HaroldMurcia/AgroSenseV1.0/Diseño/Capturas Corriente/GAS0001.BMP

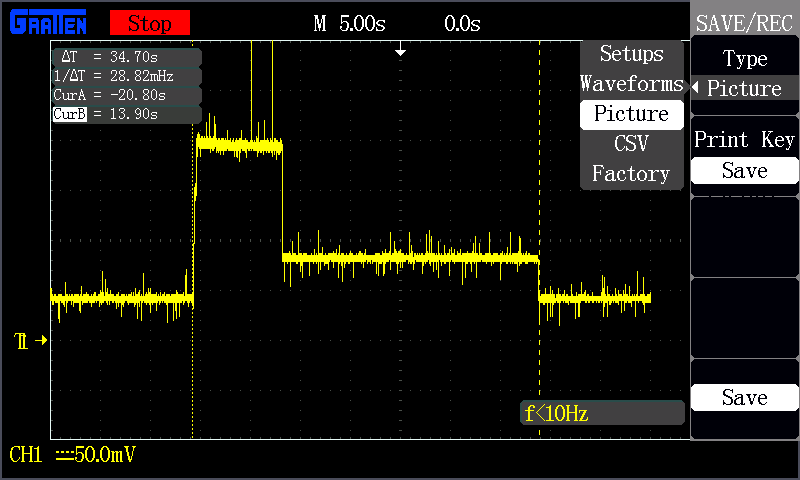
Diseño/Capturas Corriente/GAS0001.BMP
