HaroldMurcia/AgroSenseV1.0/Media/1537698291_831325_1537698456_noticia_normal.jpg

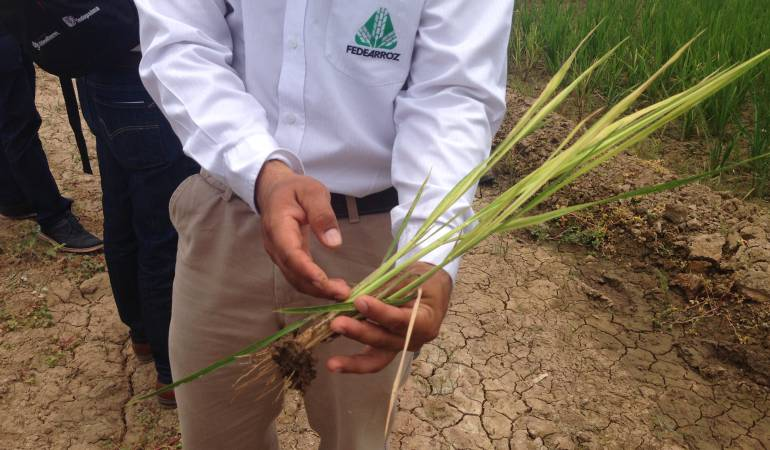
Media/1537698291_831325_1537698456_noticia_normal.jpg
