HaroldMurcia/AgroSenseV1.0/Media/1537698291_831325_1537700034_sumario_normal.jpg

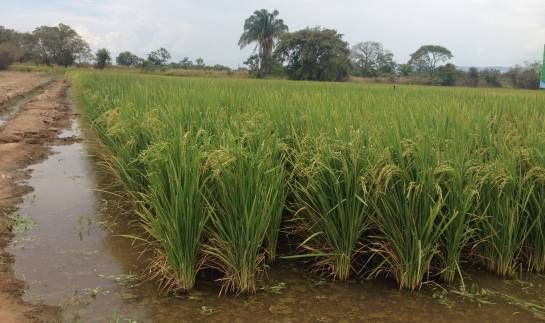
Media/1537698291_831325_1537700034_sumario_normal.jpg
