HaroldMurcia/AgroSenseV1.0/Media/AgroS.004.jpg

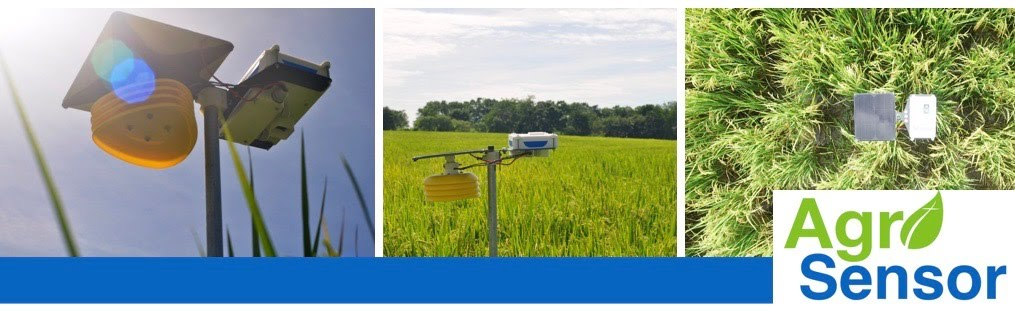
Media/AgroS.004.jpg
