HaroldMurcia/AgroSenseV1.0/Media/Agrosensor2.jpg

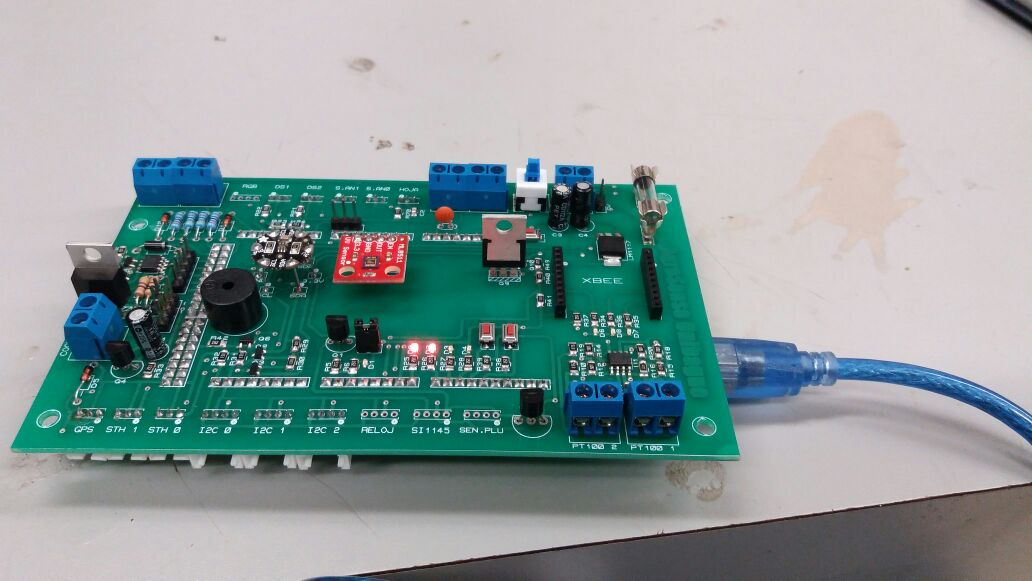
Media/Agrosensor2.jpg
