HaroldMurcia/AgroSenseV1.0/Media/Agrosensor Collector.PNG

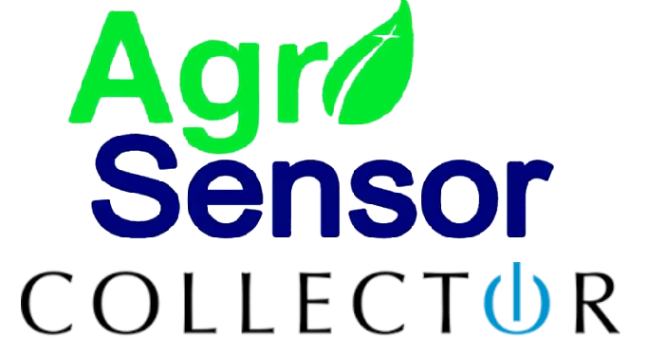
Media/Agrosensor Collector.PNG
