HaroldMurcia/AgroSenseV1.0/Media/Agrosensor.jpg

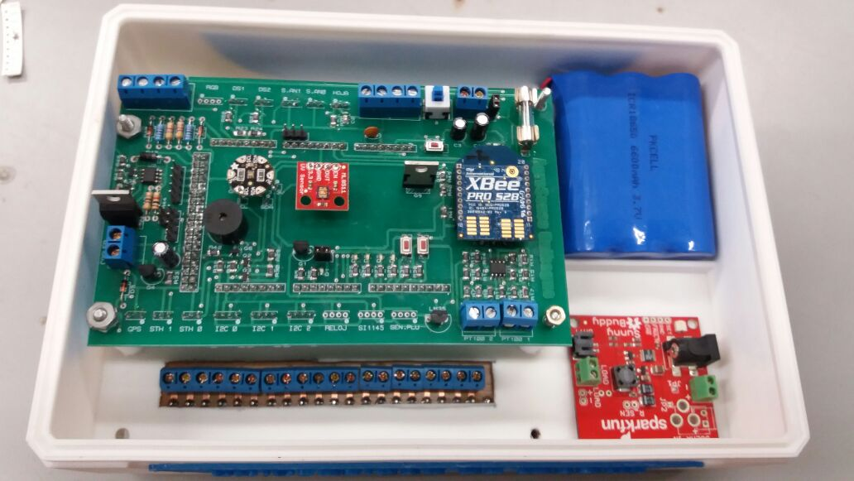
Media/Agrosensor.jpg
