HaroldMurcia/AgroSenseV1.0/Media/Configuracion XBee/Firmware Colector.jpg

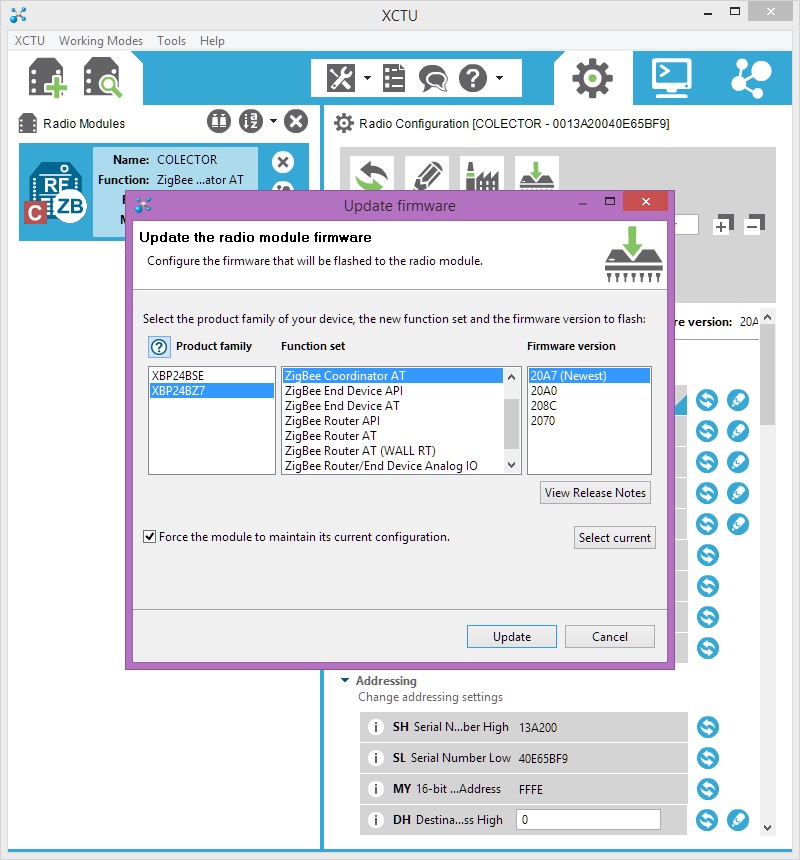
Media/Configuracion XBee/Firmware Colector.jpg
