HaroldMurcia/AgroSenseV1.0/Media/Configuracion XBee/Firmware Nodo.jpg

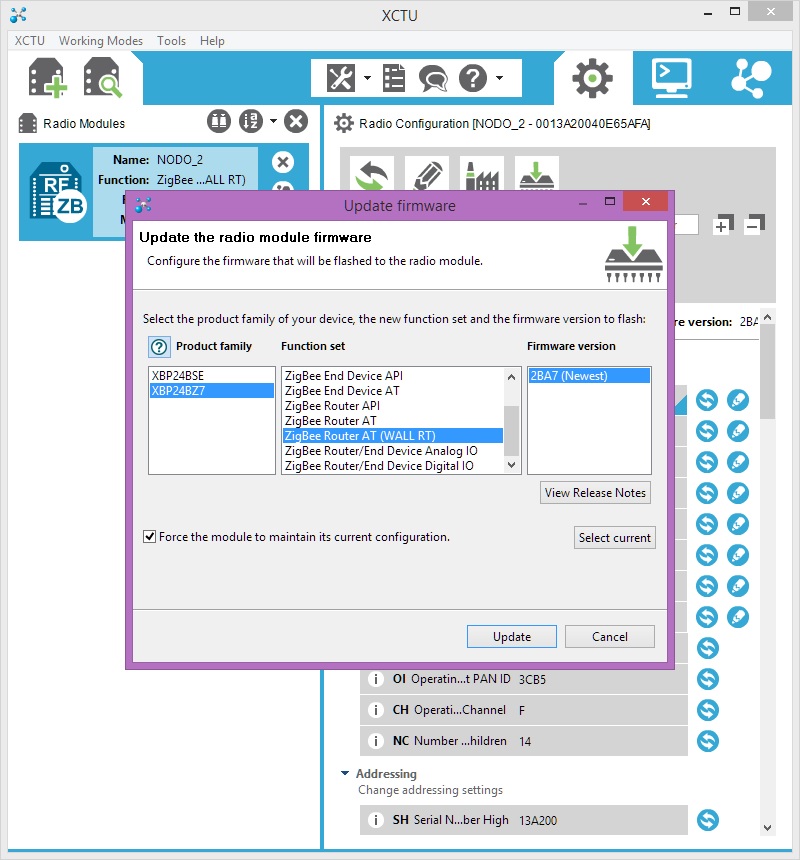
Media/Configuracion XBee/Firmware Nodo.jpg
