HaroldMurcia/AgroSenseV1.0/Media/DS18B20 grafica.jpg

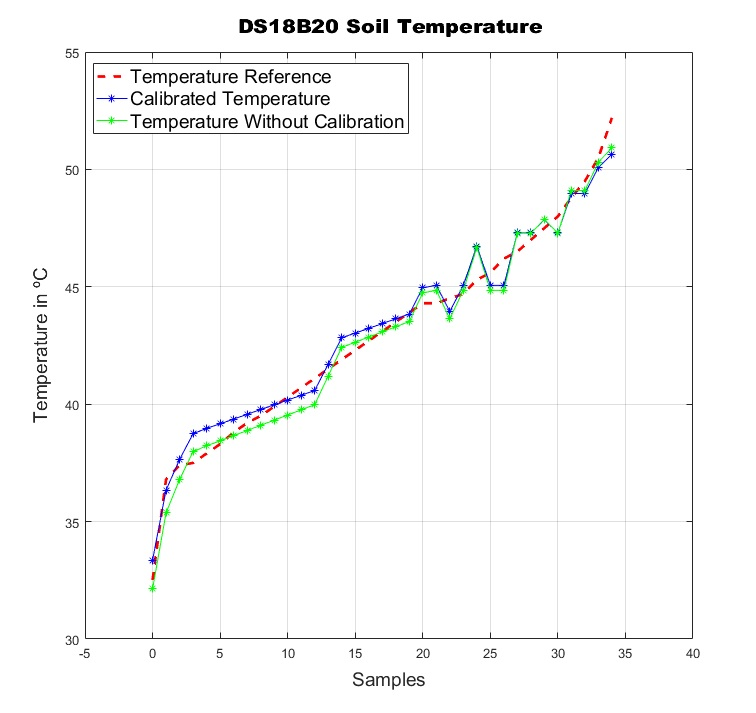
Media/DS18B20 grafica.jpg
