HaroldMurcia/AgroSenseV1.0/Media/DSC_0012.JPG

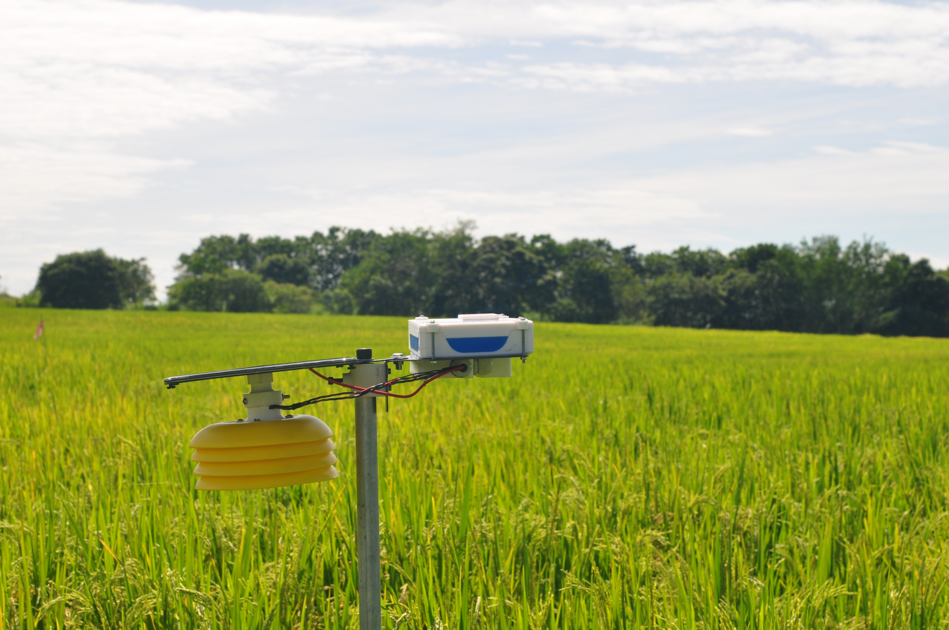
Media/DSC_0012.JPG
