HaroldMurcia/AgroSenseV1.0/Media/DSC_0013.JPG

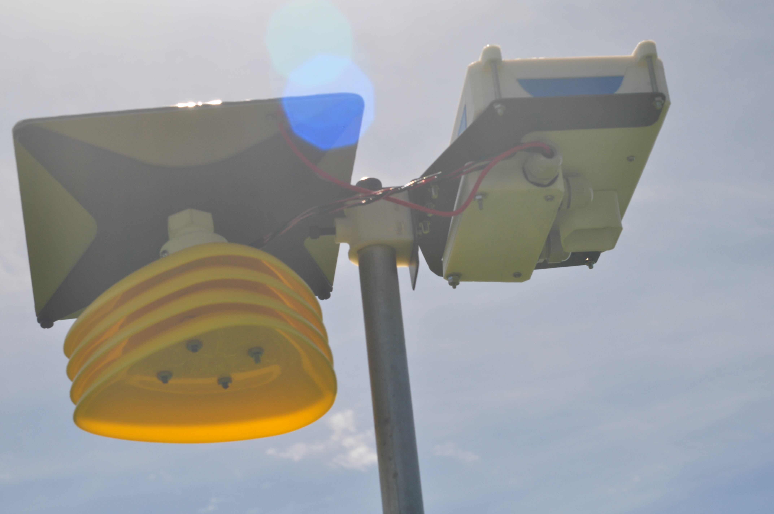
Media/DSC_0013.JPG
