HaroldMurcia/AgroSenseV1.0/Media/DSC_0014.JPG

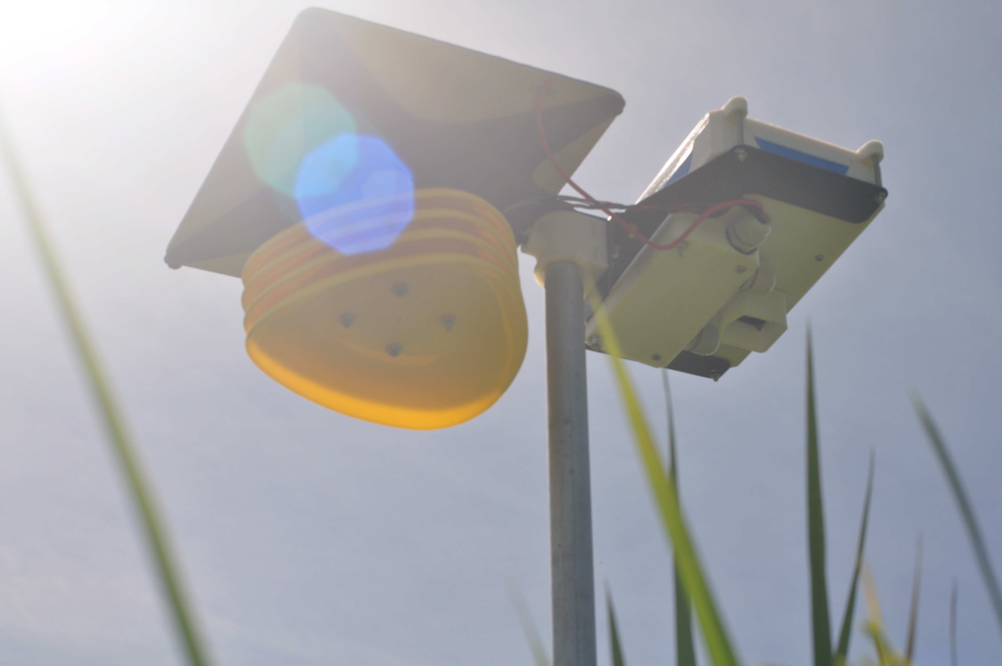
Media/DSC_0014.JPG
