HaroldMurcia/AgroSenseV1.0/Media/DSC_0015.JPG

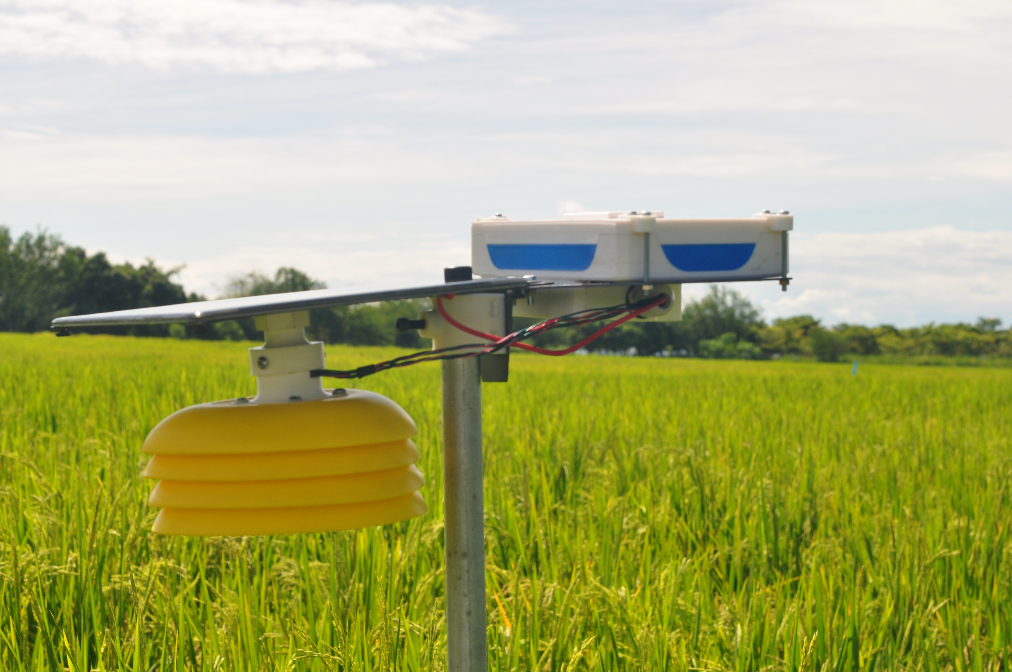
Media/DSC_0015.JPG
