HaroldMurcia/AgroSenseV1.0/Media/Fotos.jpg

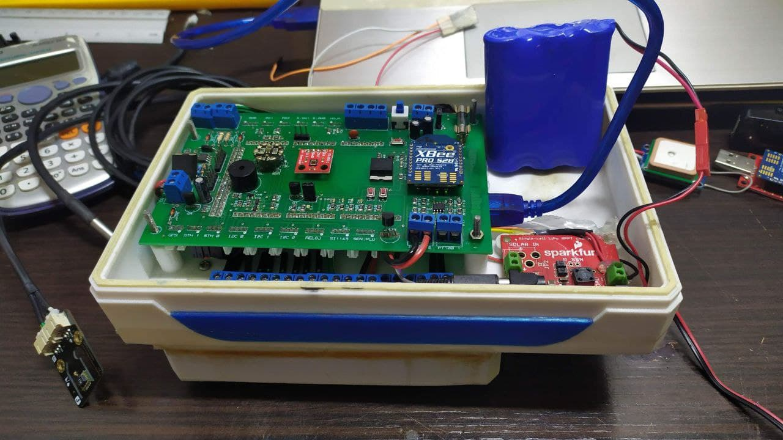
Media/Fotos.jpg
