HaroldMurcia/AgroSenseV1.0/Media/Grafica1.jpg

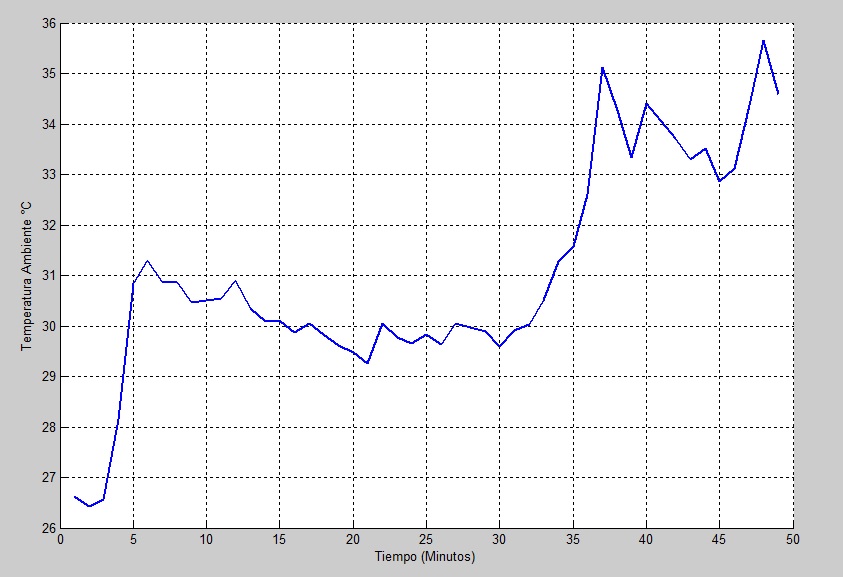
Media/Grafica1.jpg
