HaroldMurcia/AgroSenseV1.0/Media/Grafica2.jpg

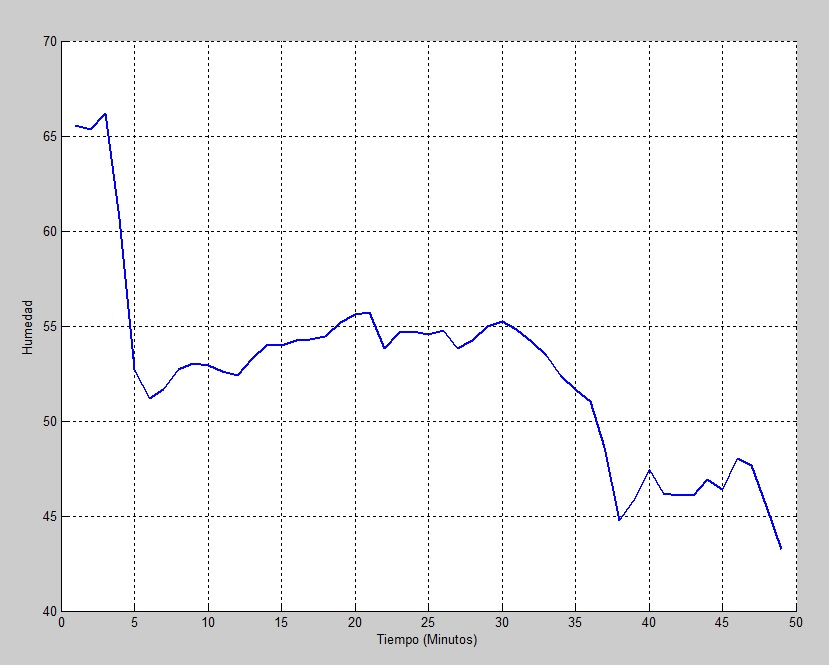
Media/Grafica2.jpg
