HaroldMurcia/AgroSenseV1.0/Media/Grafica3.jpg

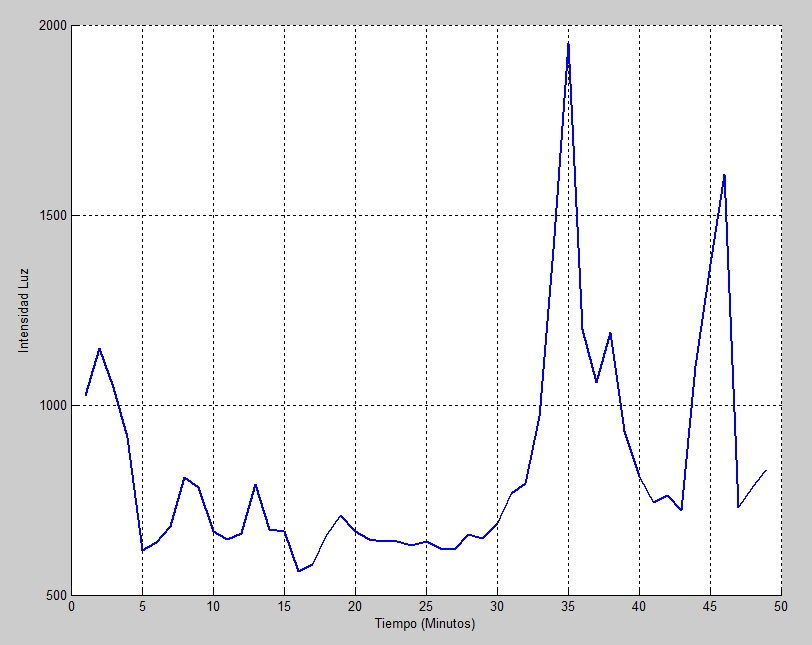
Media/Grafica3.jpg
