HaroldMurcia/AgroSenseV1.0/Media/Grafica4.jpg

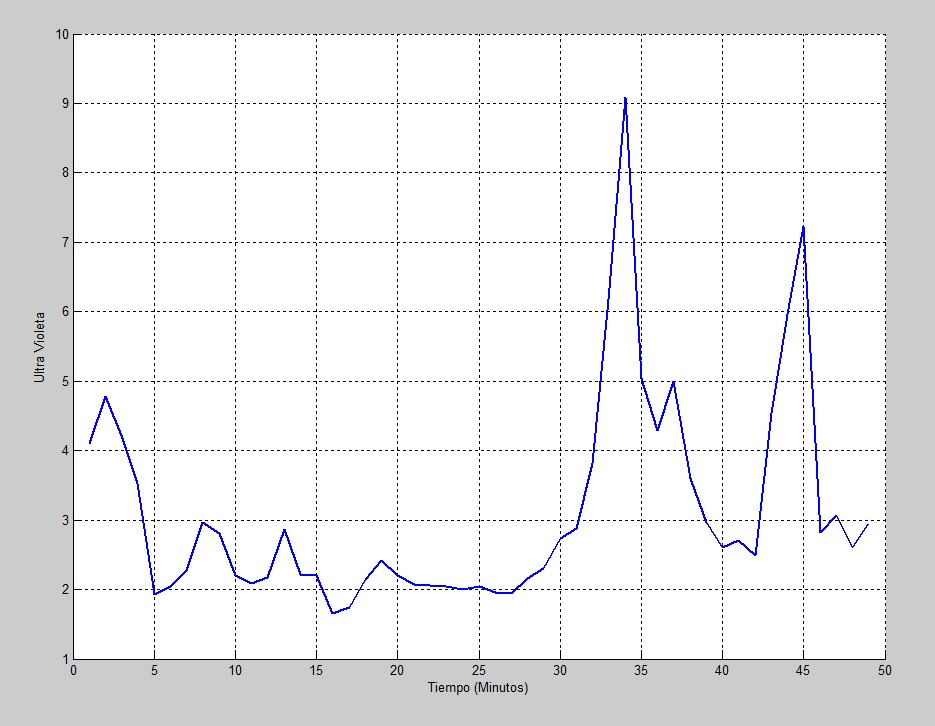
Media/Grafica4.jpg
