HaroldMurcia/AgroSenseV1.0/Media/Grafica IV Panel.bmp

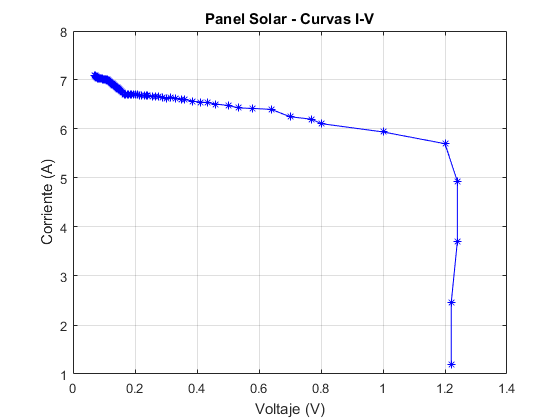
Media/Grafica IV Panel.bmp
