HaroldMurcia/AgroSenseV1.0/Media/image (1).png

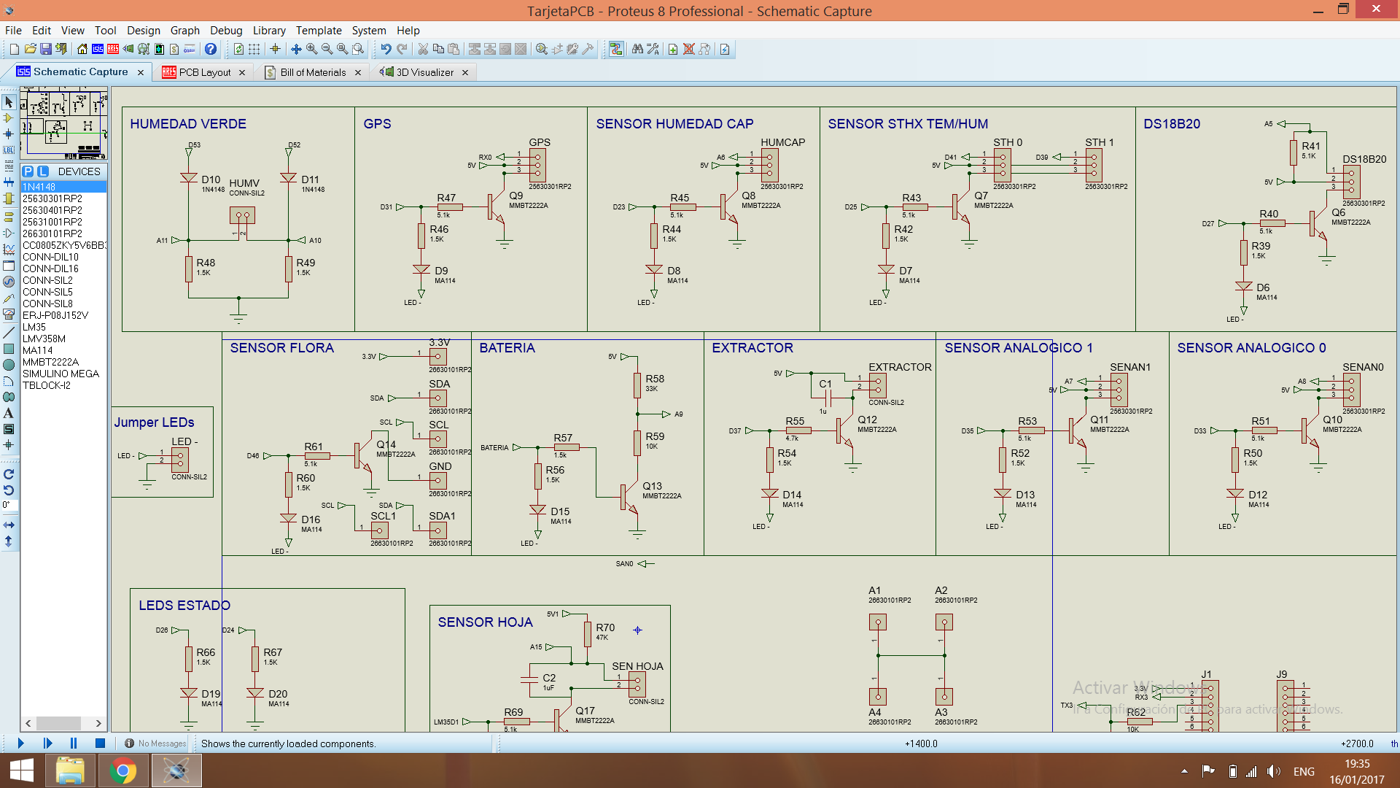
Media/image (1).png
