HaroldMurcia/AgroSenseV1.0/Media/image (2).png

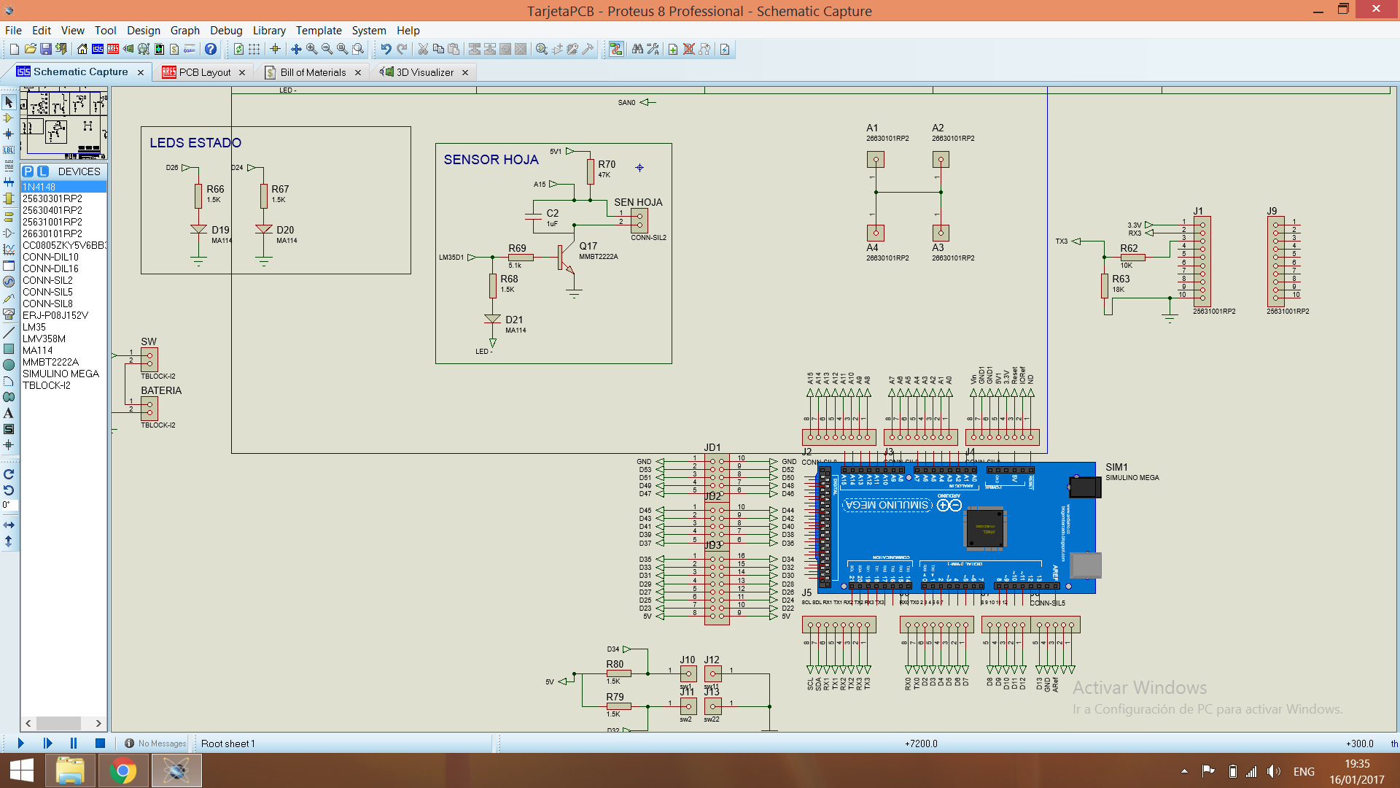
Media/image (2).png
