HaroldMurcia/AgroSenseV1.0/Media/image.png

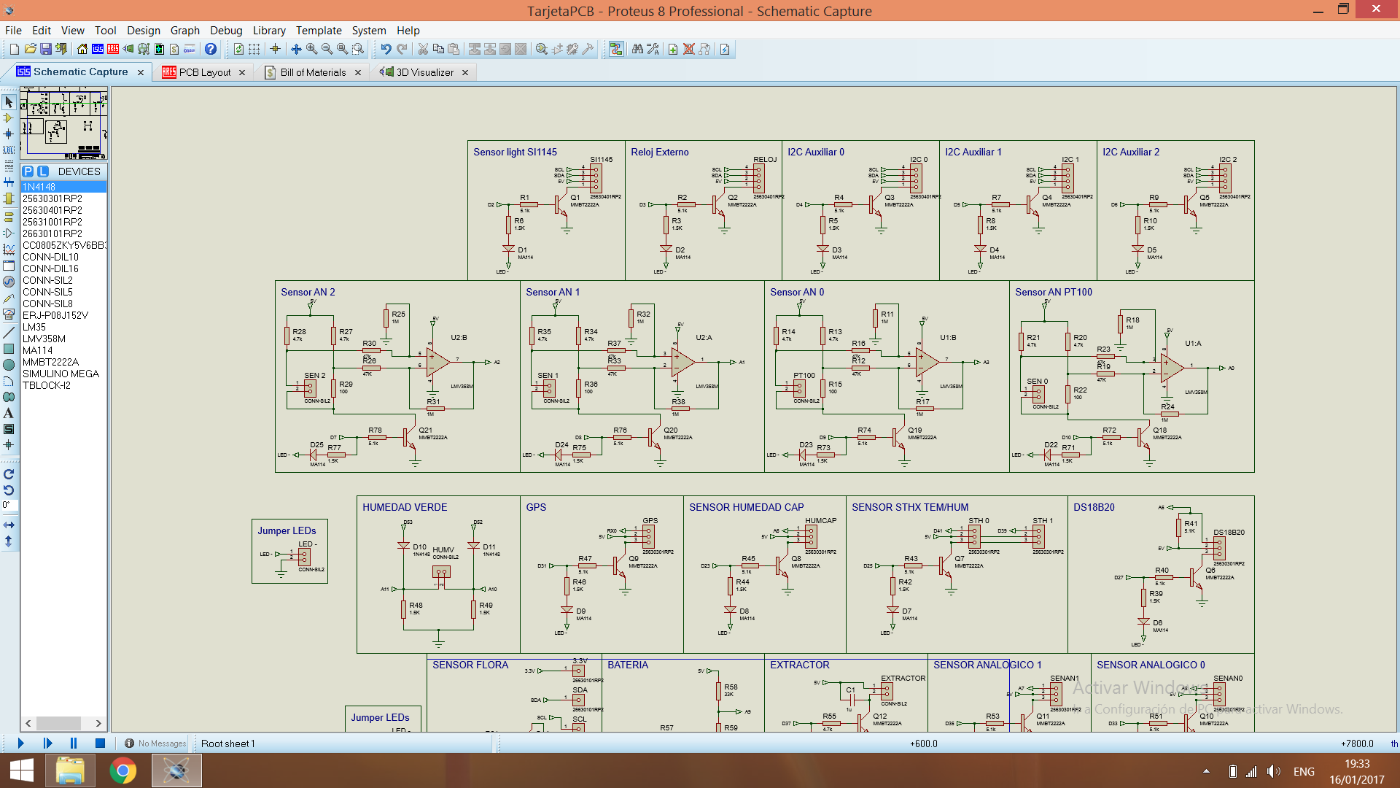
Media/image.png
