HaroldMurcia/AgroSenseV1.0/Media/IMG_3761.jpg

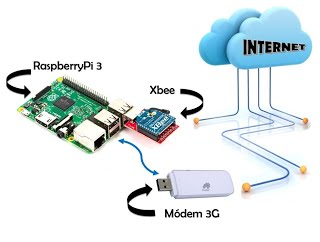
Media/IMG_3761.jpg
