HaroldMurcia/AgroSenseV1.0/Media/Mapa.png

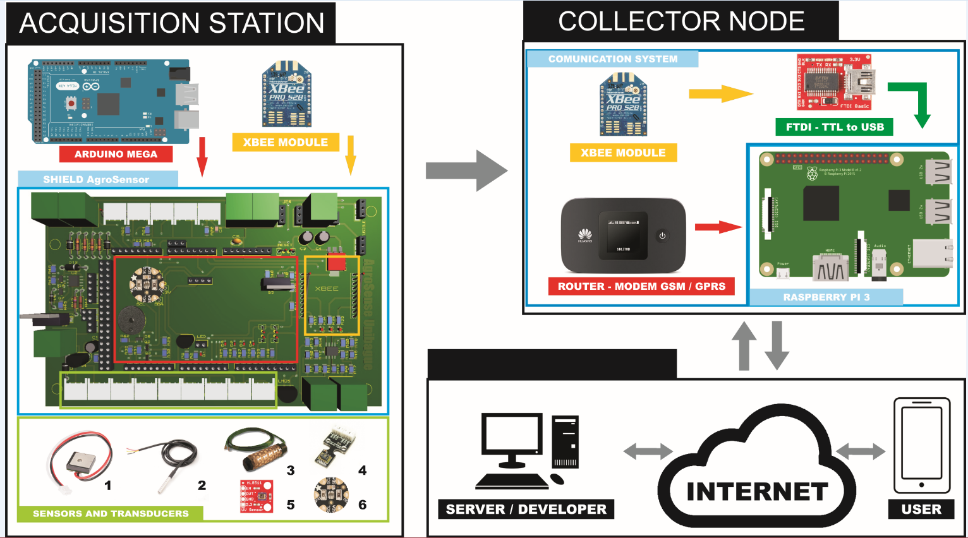
Media/Mapa.png
