HaroldMurcia/AgroSenseV1.0/Media/photo_2021-04-07_22-17-04.jpg

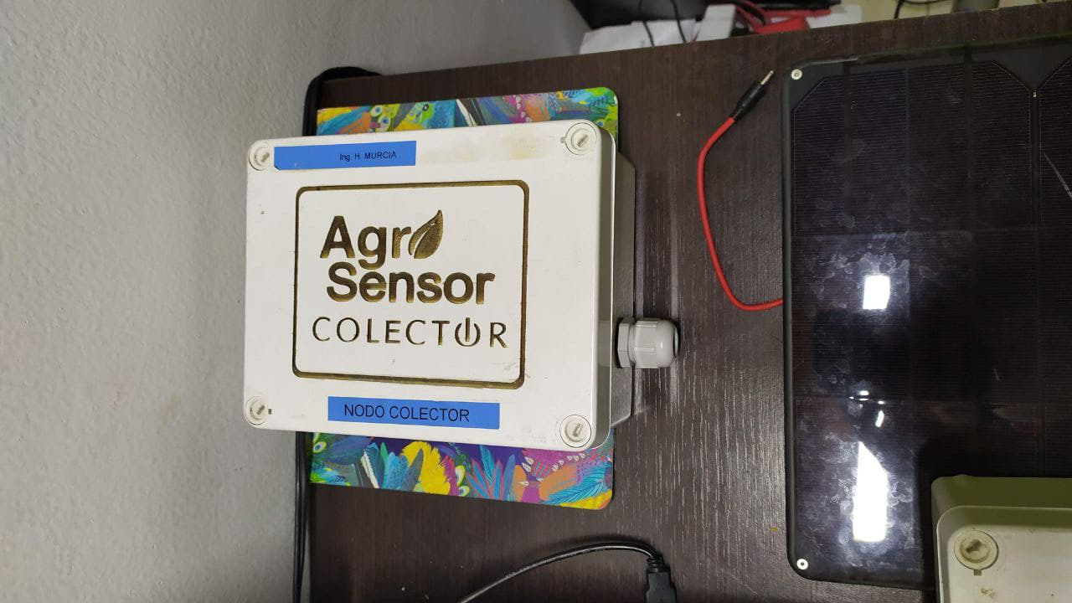
Media/photo_2021-04-07_22-17-04.jpg
