HaroldMurcia/AgroSenseV1.0/Media/Potencia.jpg

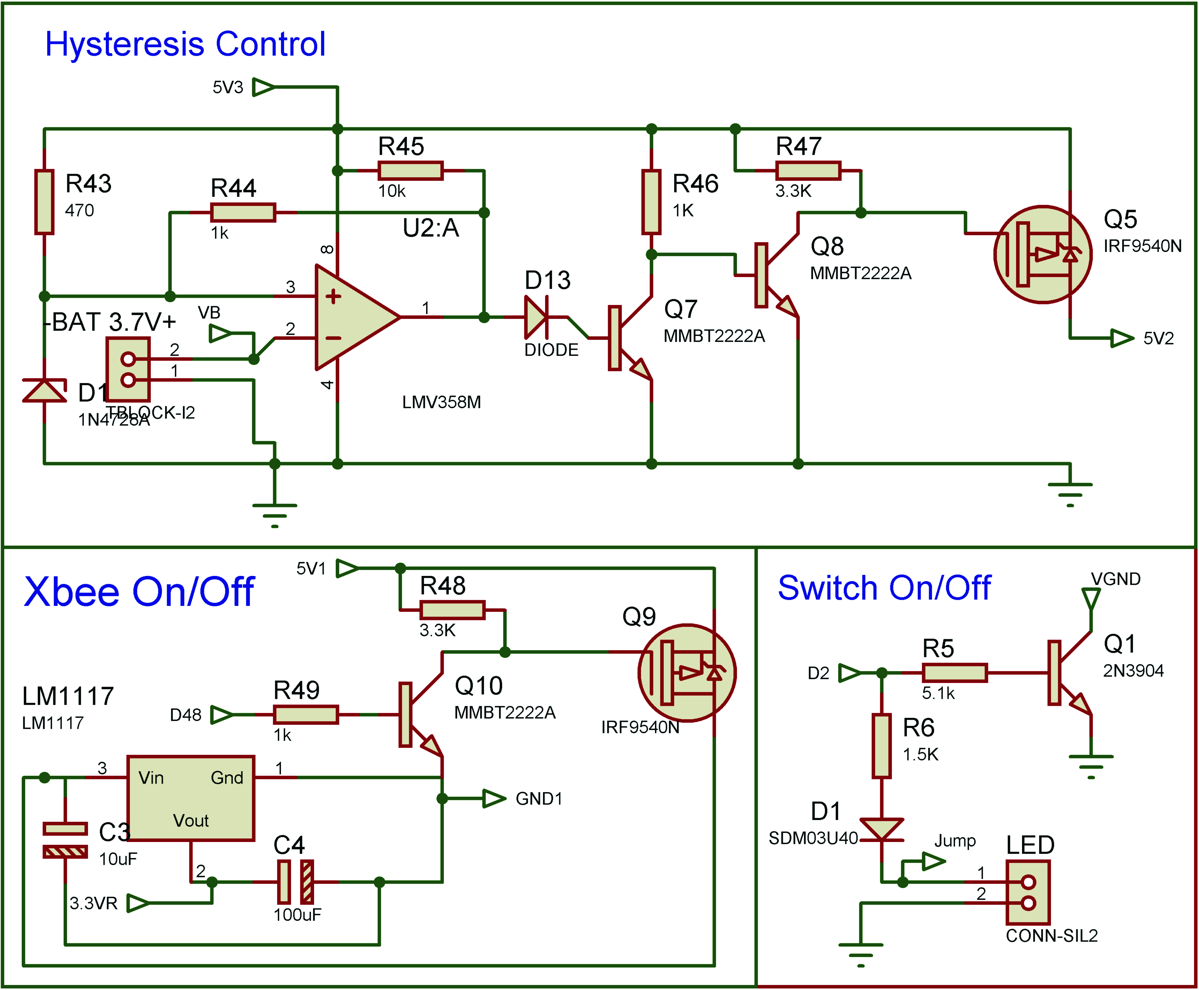
Media/Potencia.jpg
