HaroldMurcia/AgroSenseV1.0/Media/Prototipos/Codigo yowsup.png

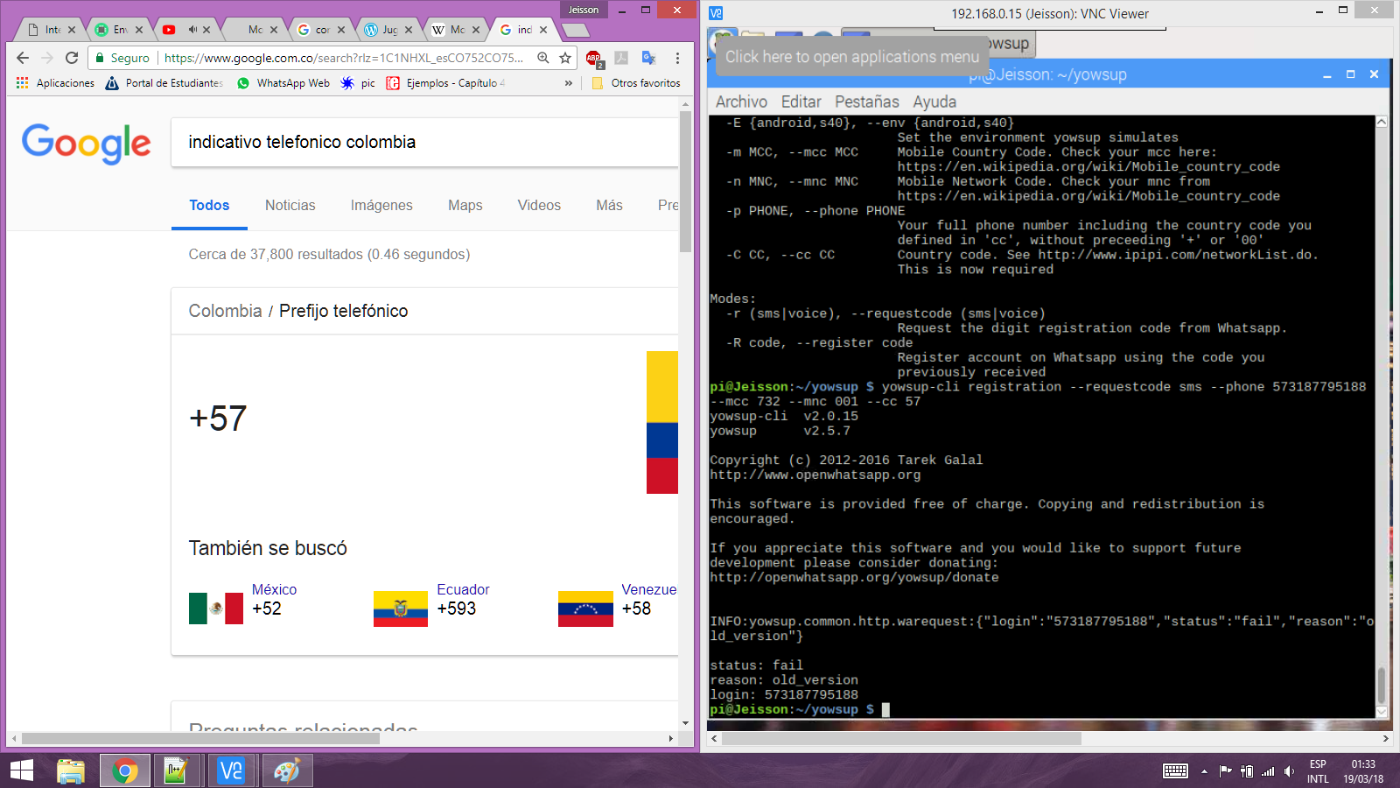
Media/Prototipos/Codigo yowsup.png
