HaroldMurcia/AgroSenseV1.0/Media/Prototipos/datod1.png

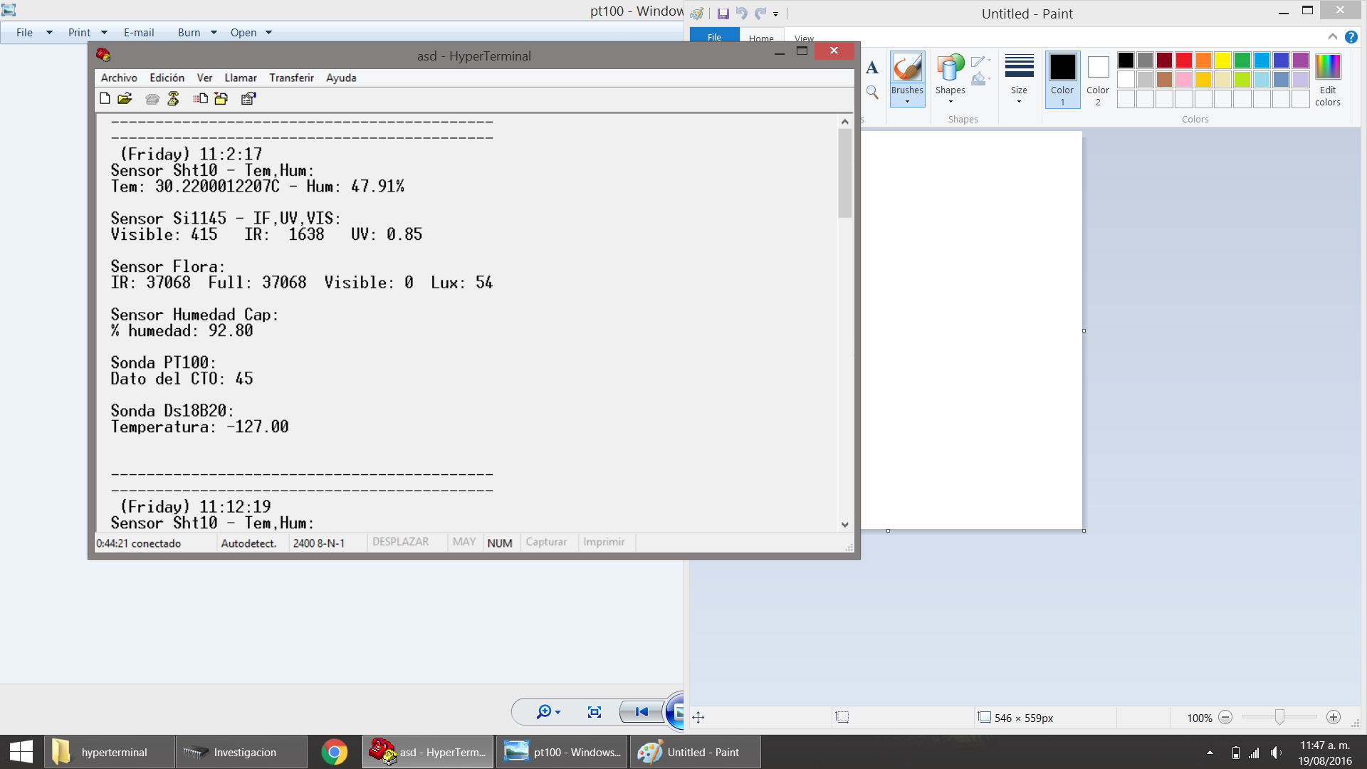
Media/Prototipos/datod1.png
