HaroldMurcia/AgroSenseV1.0/Media/Prototipos/datod2.png

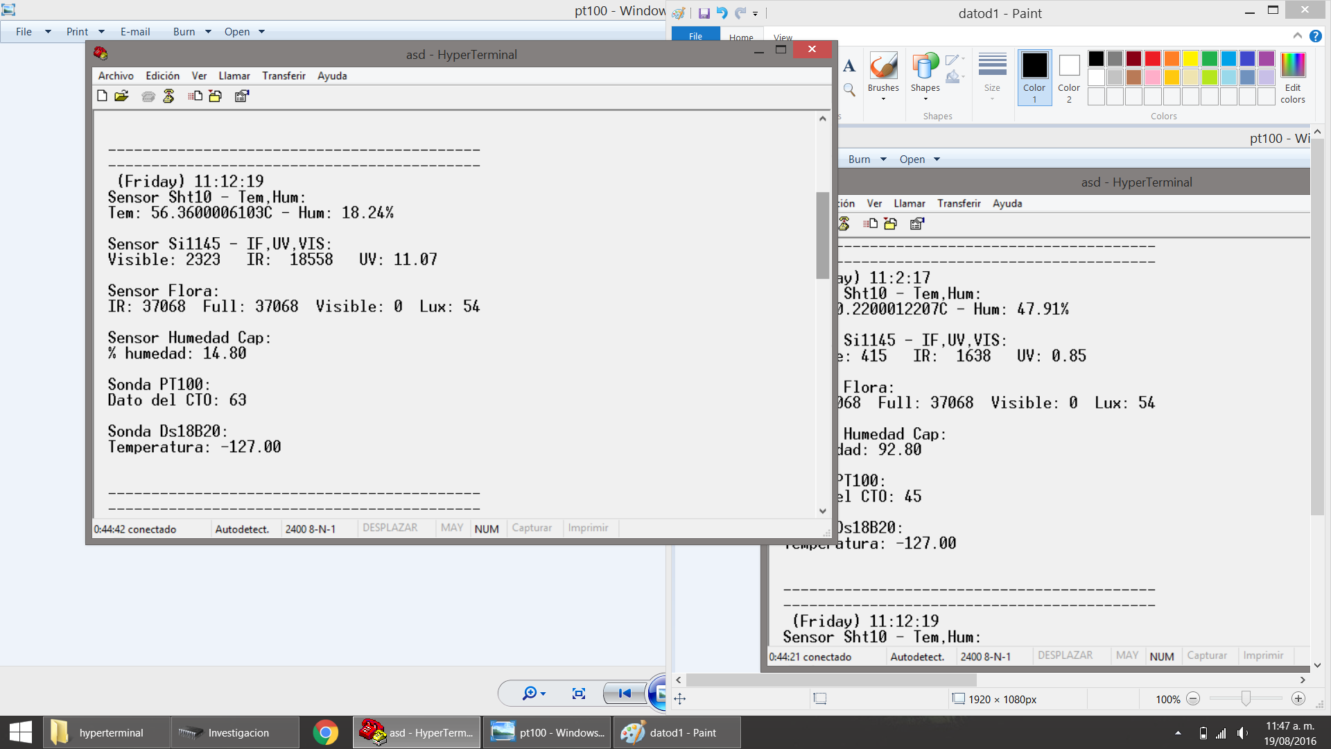
Media/Prototipos/datod2.png
