HaroldMurcia/AgroSenseV1.0/Media/Prototipos/datod3.png

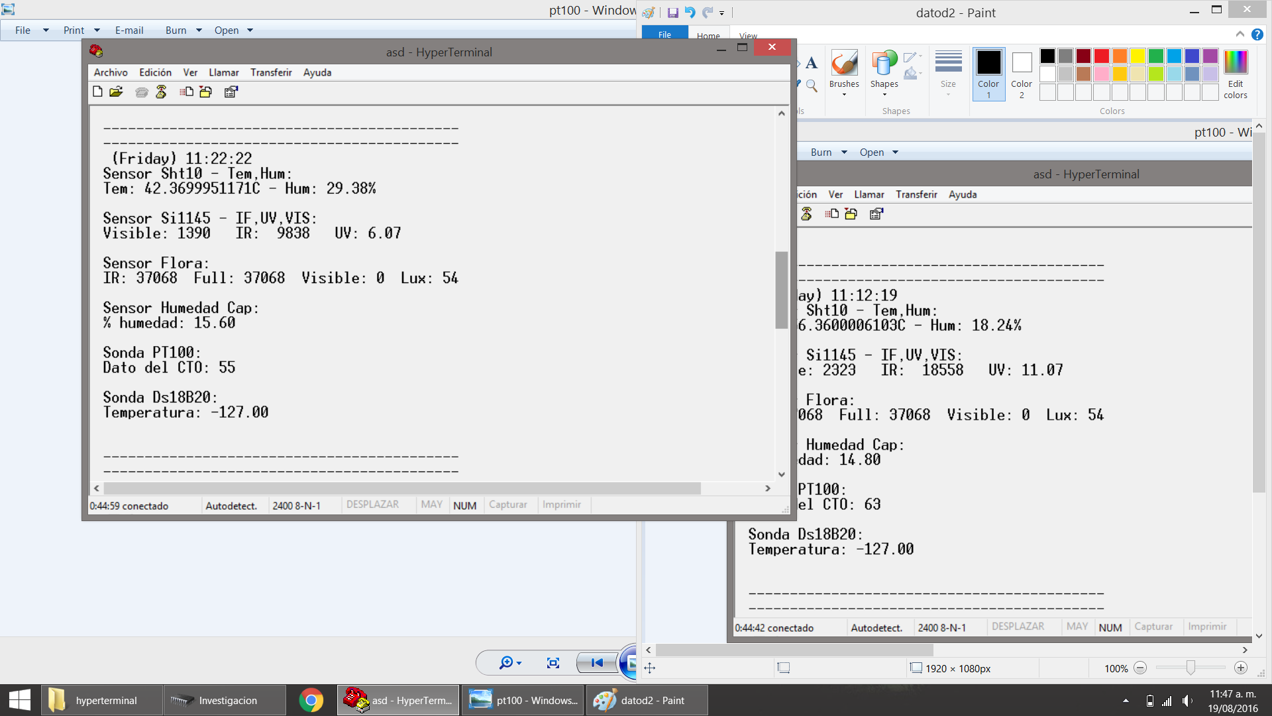
Media/Prototipos/datod3.png
