HaroldMurcia/AgroSenseV1.0/Media/Prototipos/datod5.png

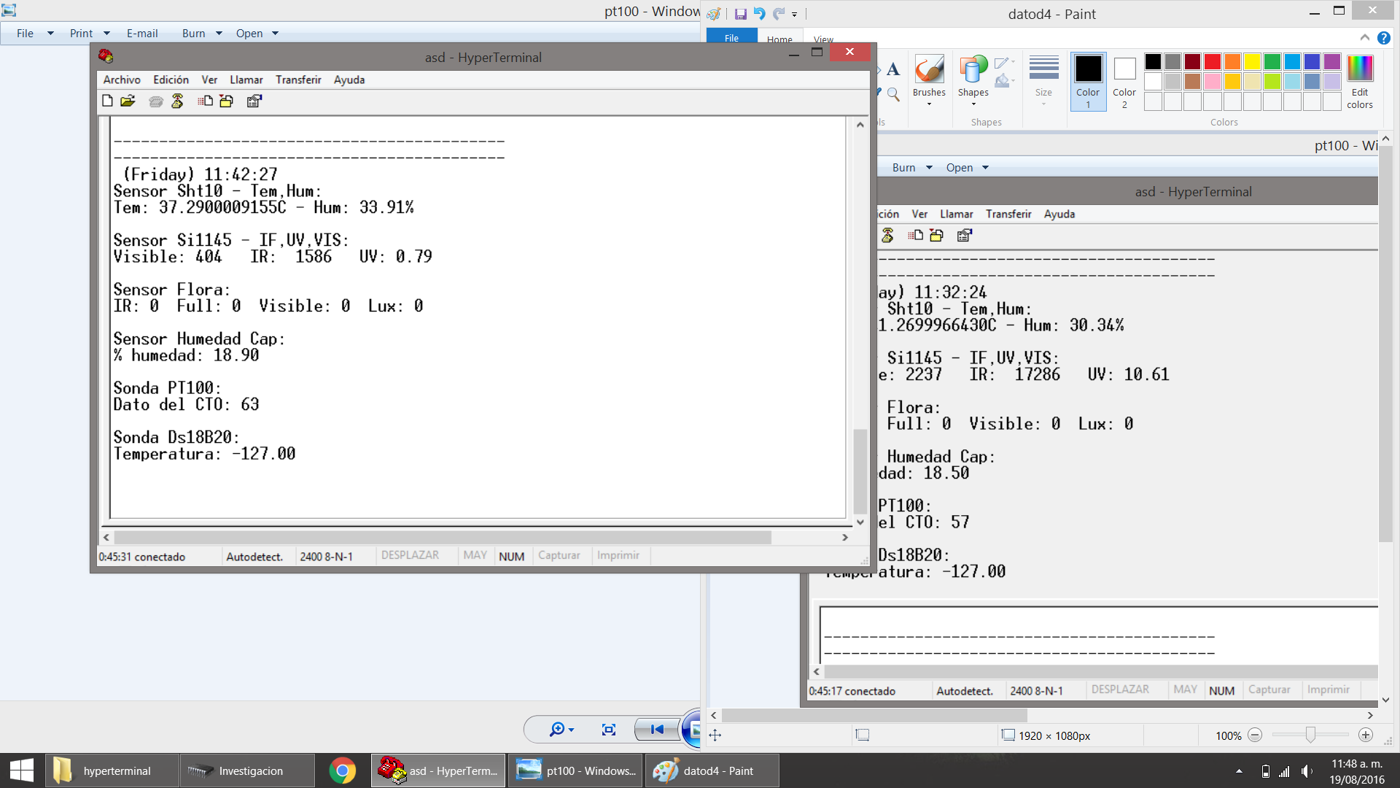
Media/Prototipos/datod5.png
