HaroldMurcia/AgroSenseV1.0/Media/Prototipos/Datos1.jpg

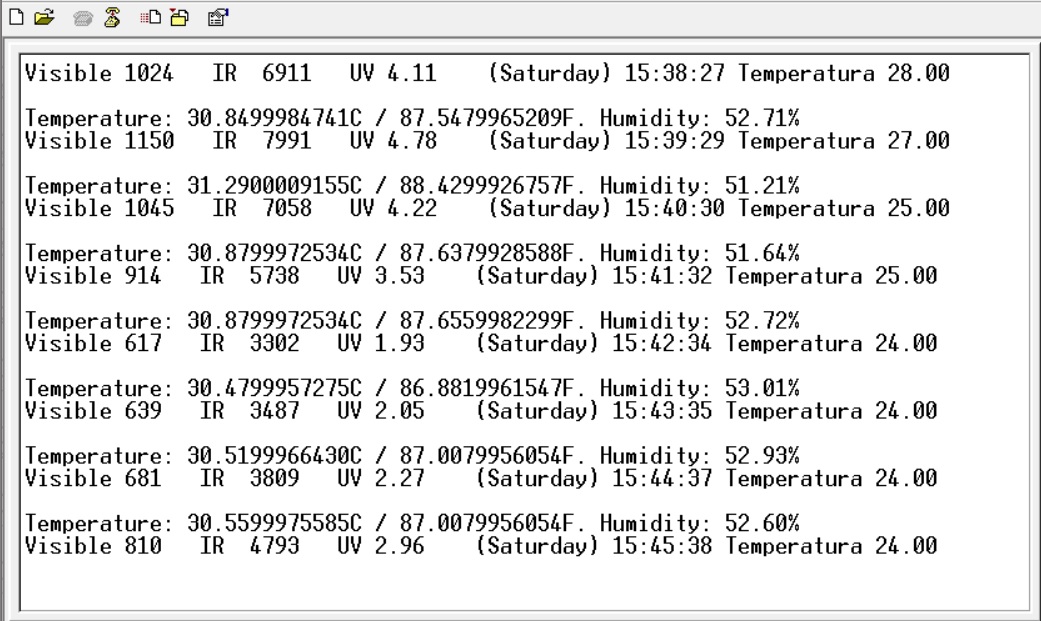
Media/Prototipos/Datos1.jpg
