HaroldMurcia/AgroSenseV1.0/Media/Prototipos/Datos2.jpg

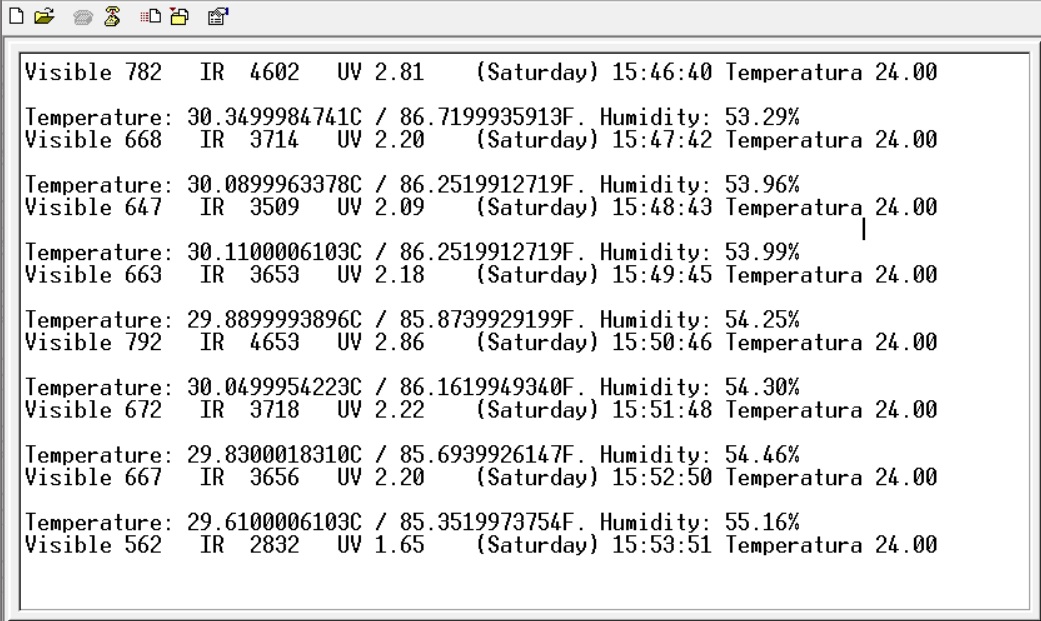
Media/Prototipos/Datos2.jpg
