HaroldMurcia/AgroSenseV1.0/Media/Prototipos/Diagrama 2.jpg

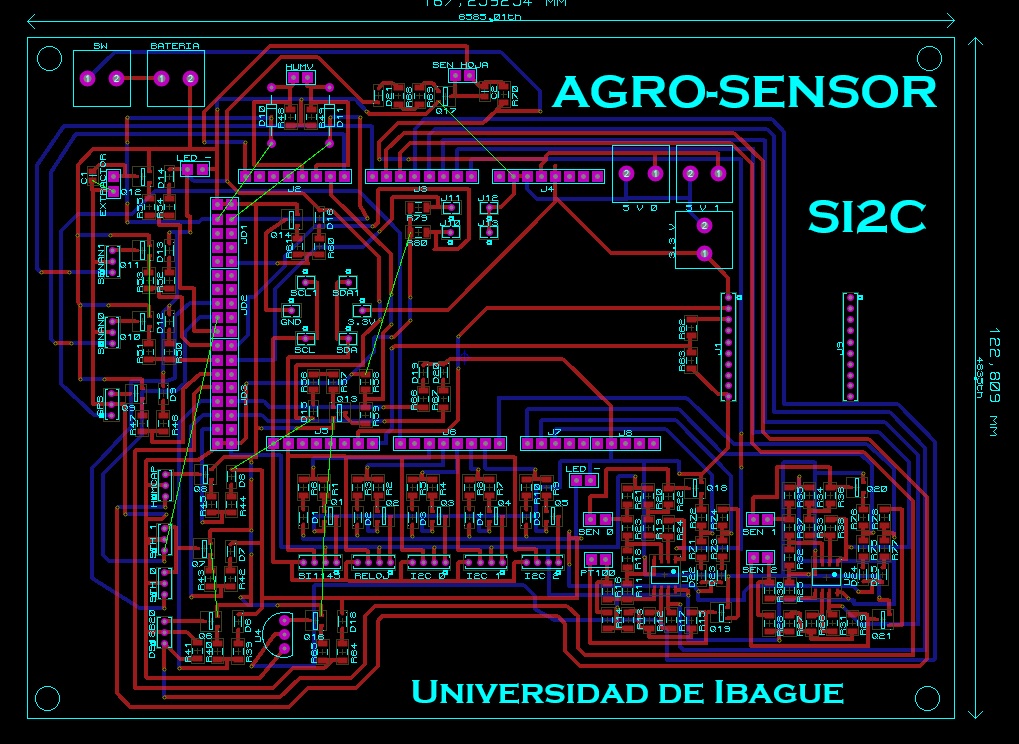
Media/Prototipos/Diagrama 2.jpg
