HaroldMurcia/AgroSenseV1.0/Media/Prototipos/Diagrama.jpg

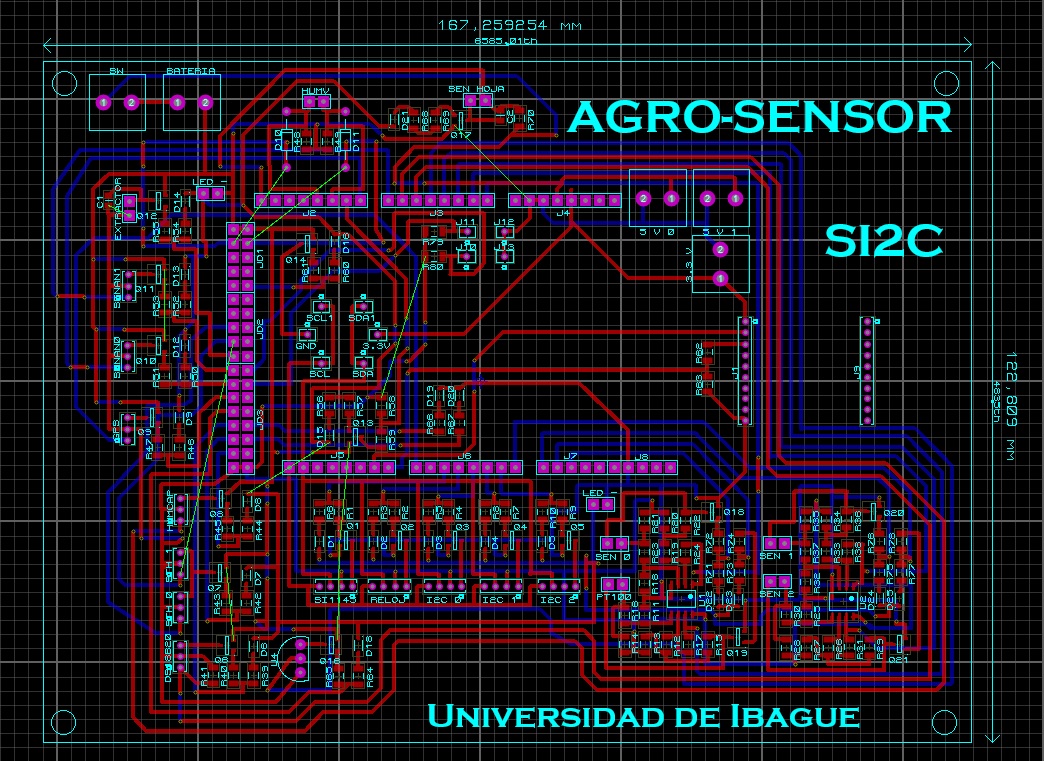
Media/Prototipos/Diagrama.jpg
