HaroldMurcia/AgroSenseV1.0/Media/Prototipos/Esquema 1.jpg

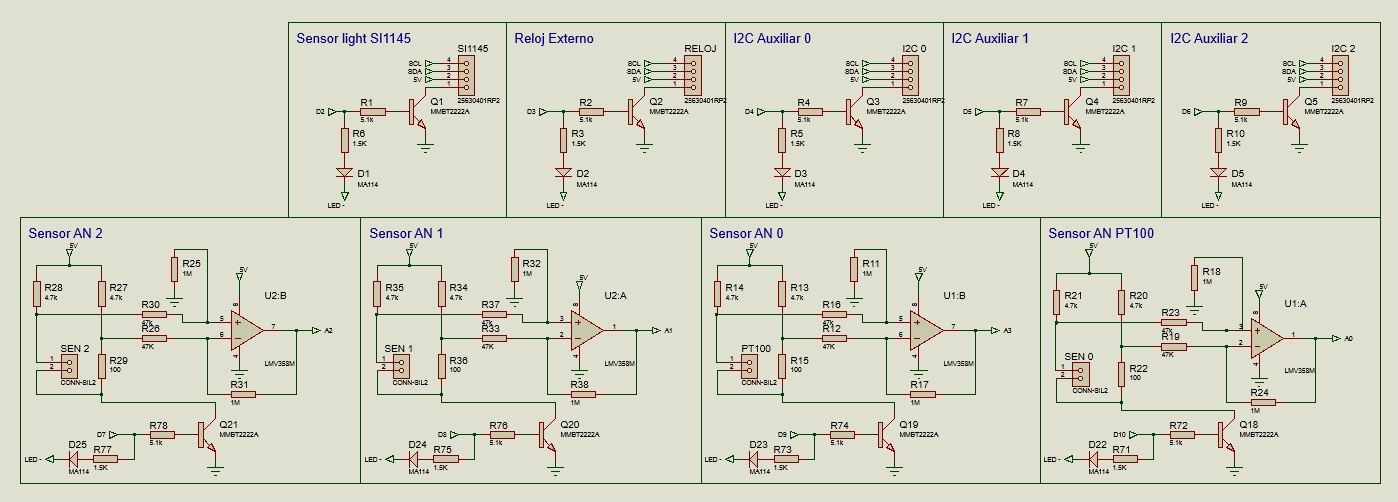
Media/Prototipos/Esquema 1.jpg
