HaroldMurcia/AgroSenseV1.0/Media/Prototipos/Esquema 2.jpg

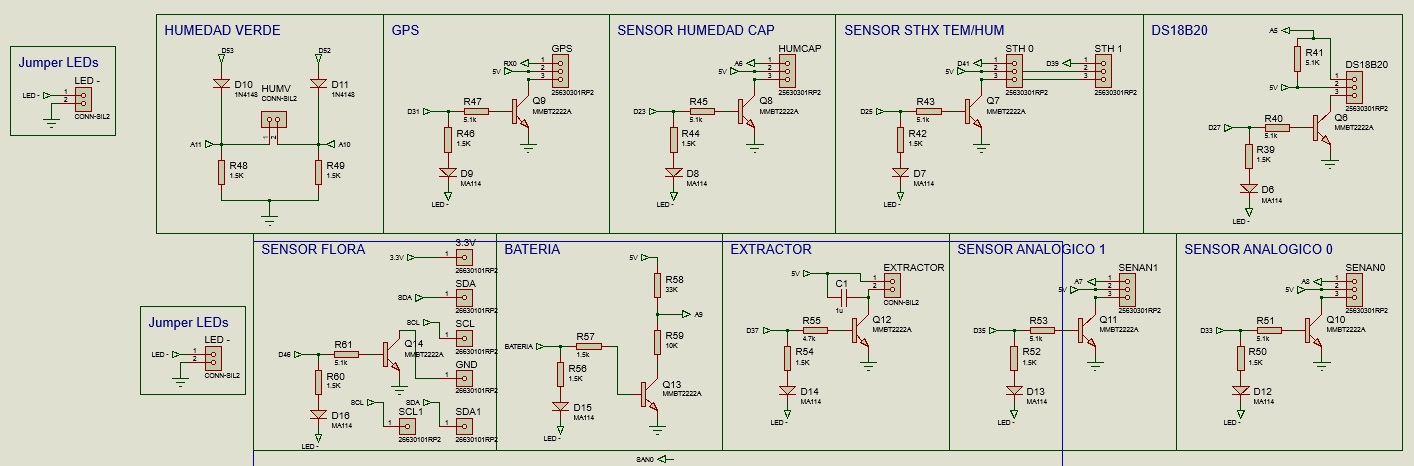
Media/Prototipos/Esquema 2.jpg
