HaroldMurcia/AgroSenseV1.0/Media/Prototipos/Esquema 3.jpg

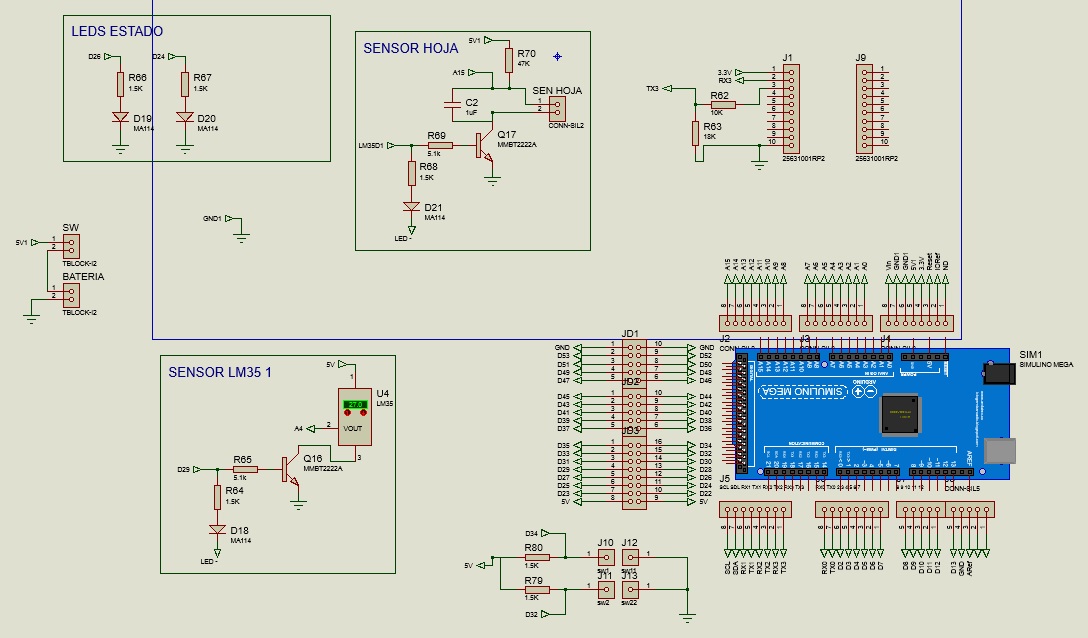
Media/Prototipos/Esquema 3.jpg
