HaroldMurcia/AgroSenseV1.0/Media/Prototipos/Fisico 1.jpg

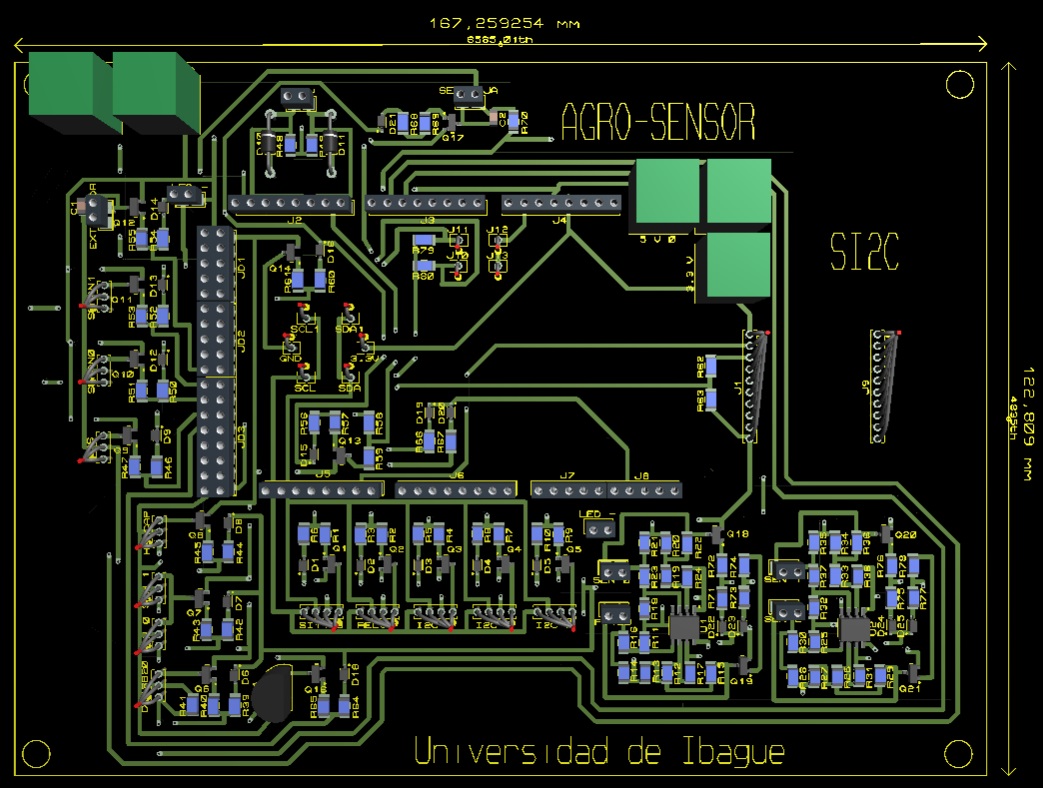
Media/Prototipos/Fisico 1.jpg
