HaroldMurcia/AgroSenseV1.0/Media/Prototipos/Fisico 2.jpg

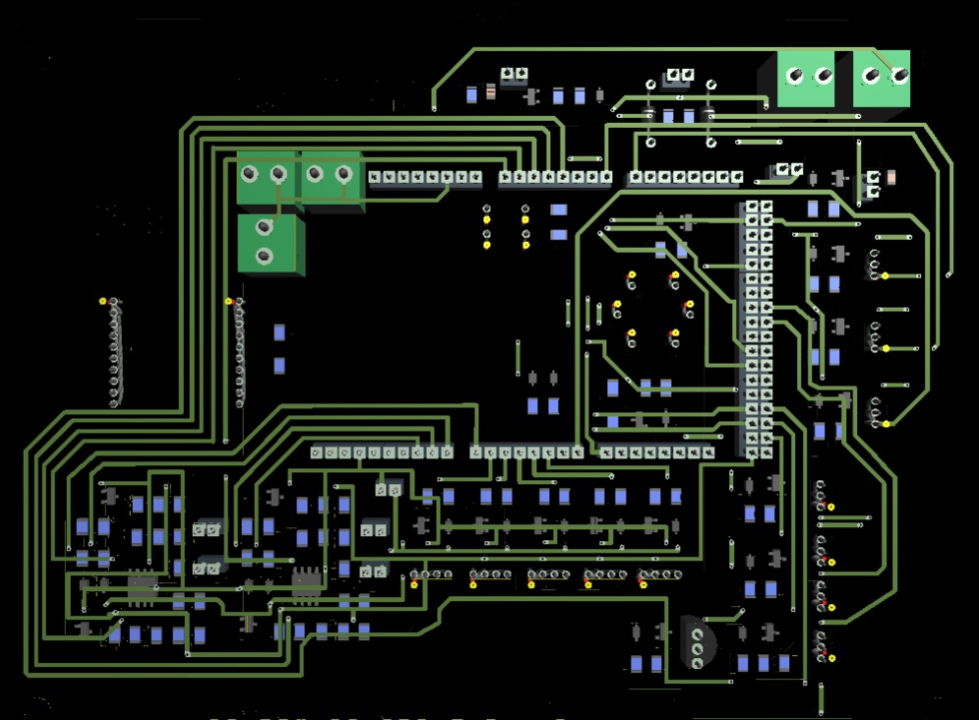
Media/Prototipos/Fisico 2.jpg
