HaroldMurcia/AgroSenseV1.0/Media/Prototipos/Fisico 3.jpg

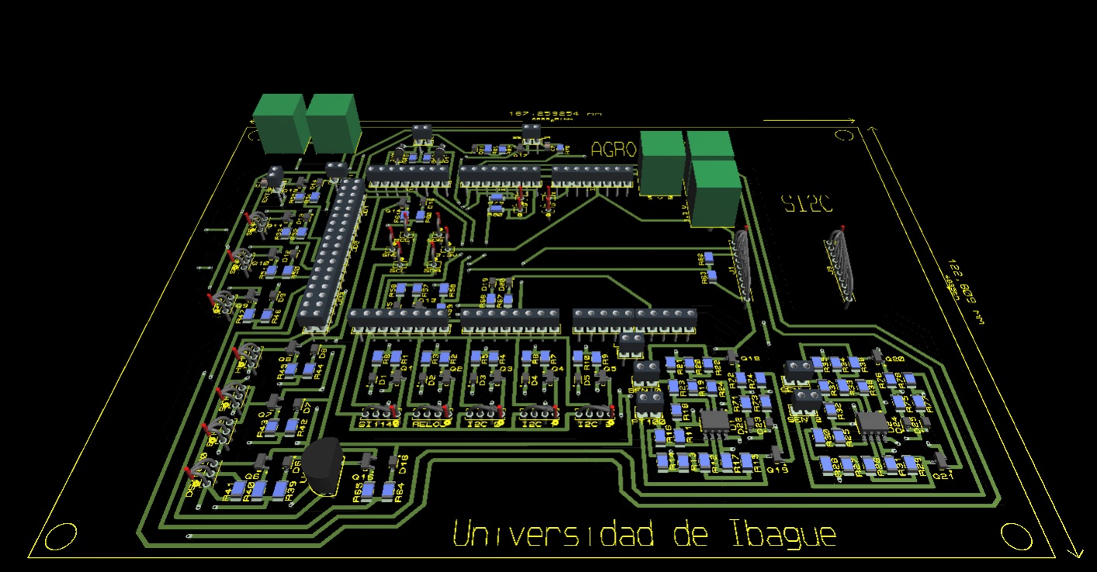
Media/Prototipos/Fisico 3.jpg
