HaroldMurcia/AgroSenseV1.0/Media/Prototipos/Imagen1.jpg

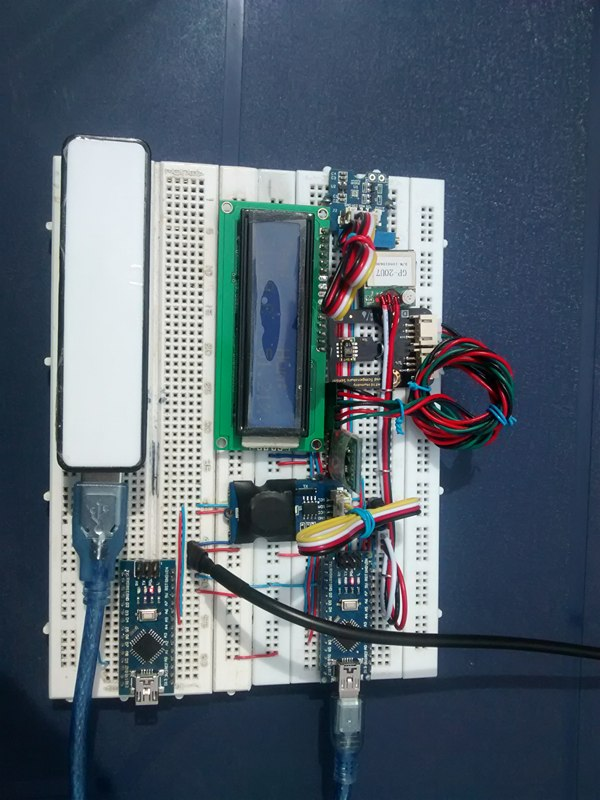
Media/Prototipos/Imagen1.jpg
