HaroldMurcia/AgroSenseV1.0/Media/Prototipos/Imagen2.jpg

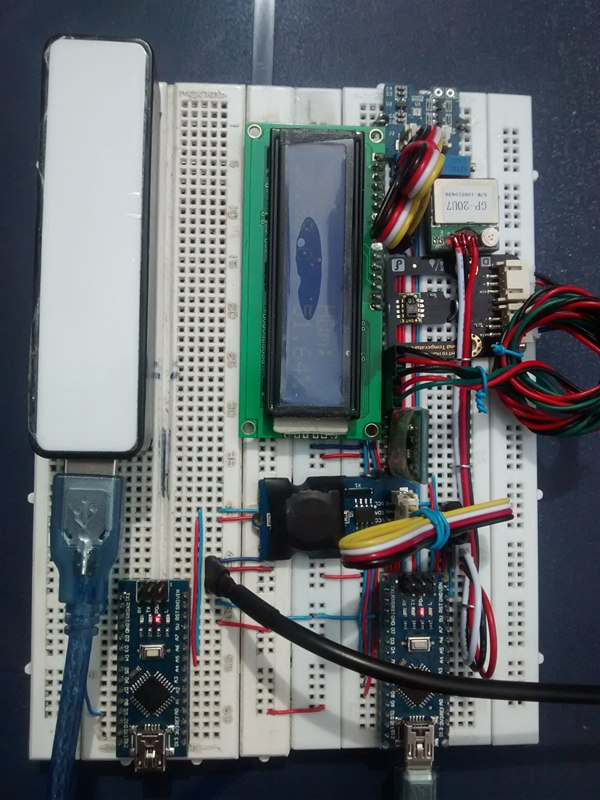
Media/Prototipos/Imagen2.jpg
