HaroldMurcia/AgroSenseV1.0/Media/Prototipos/Imagen3.jpg

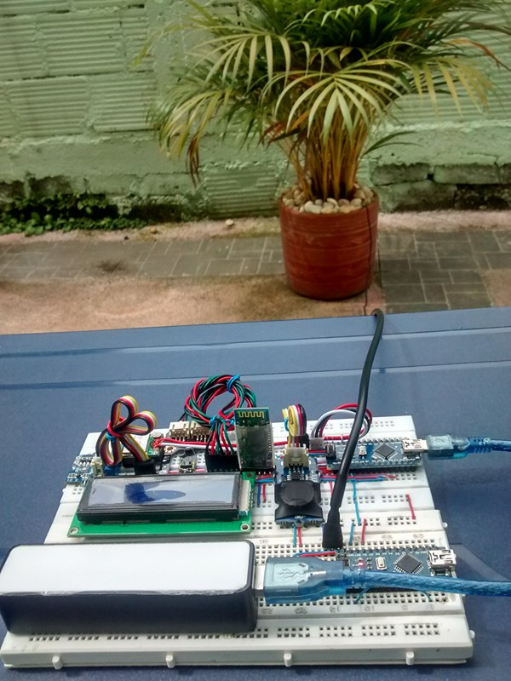
Media/Prototipos/Imagen3.jpg
