HaroldMurcia/AgroSenseV1.0/Media/Prototipos/Imagen4.jpg

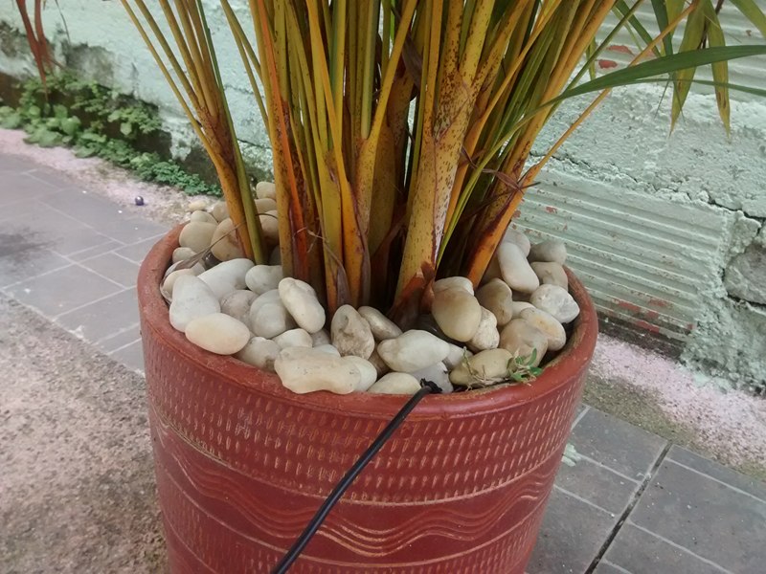
Media/Prototipos/Imagen4.jpg
