HaroldMurcia/AgroSenseV1.0/Media/Prototipos/Imagen5.jpg

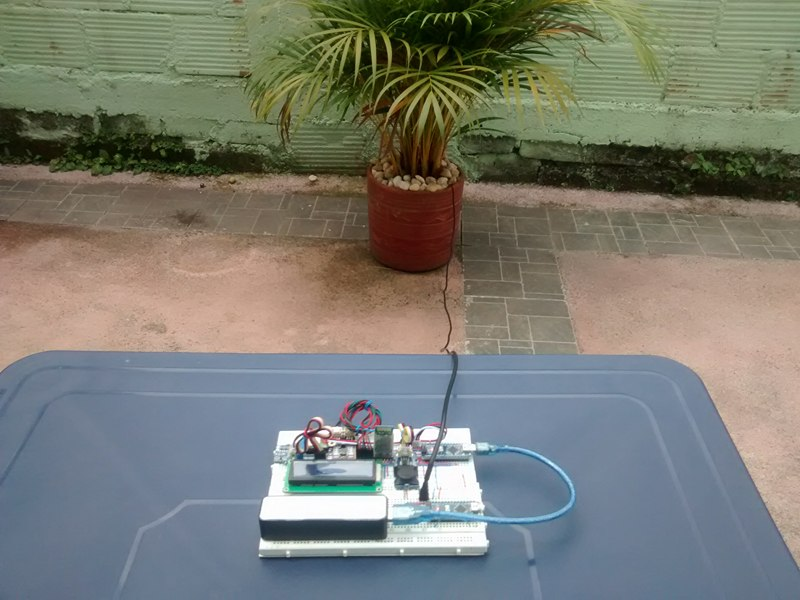
Media/Prototipos/Imagen5.jpg
