HaroldMurcia/AgroSenseV1.0/Media/Prototipos/received_10210566543860821.jpeg

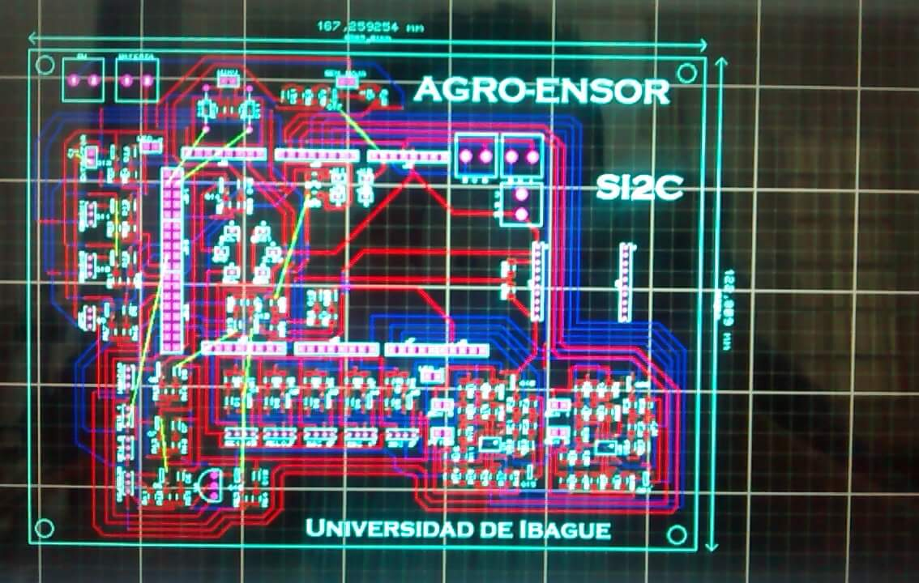
Media/Prototipos/received_10210566543860821.jpeg
