HaroldMurcia/AgroSenseV1.0/Media/pt100.png

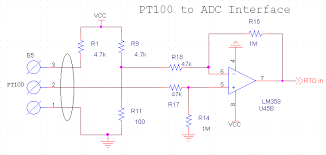
Media/pt100.png
