HaroldMurcia/AgroSenseV1.0/Media/SCOPE_00.GIF

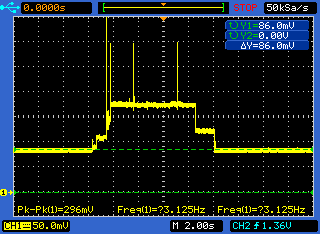
Media/SCOPE_00.GIF
