HaroldMurcia/AgroSenseV1.0/Media/Screen Shot 2017-06-25 at 9.43.59 PM.png

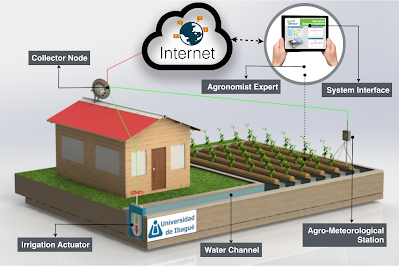
Media/Screen Shot 2017-06-25 at 9.43.59 PM.png
