HaroldMurcia/AgroSenseV1.0/Media/Sensor hoja.jpg

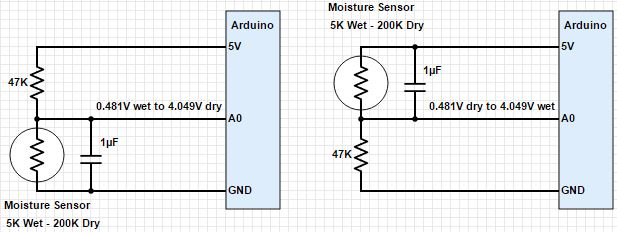
Media/Sensor hoja.jpg
