HaroldMurcia/AgroSenseV1.0/Media/Tabla_Fedearroz.png

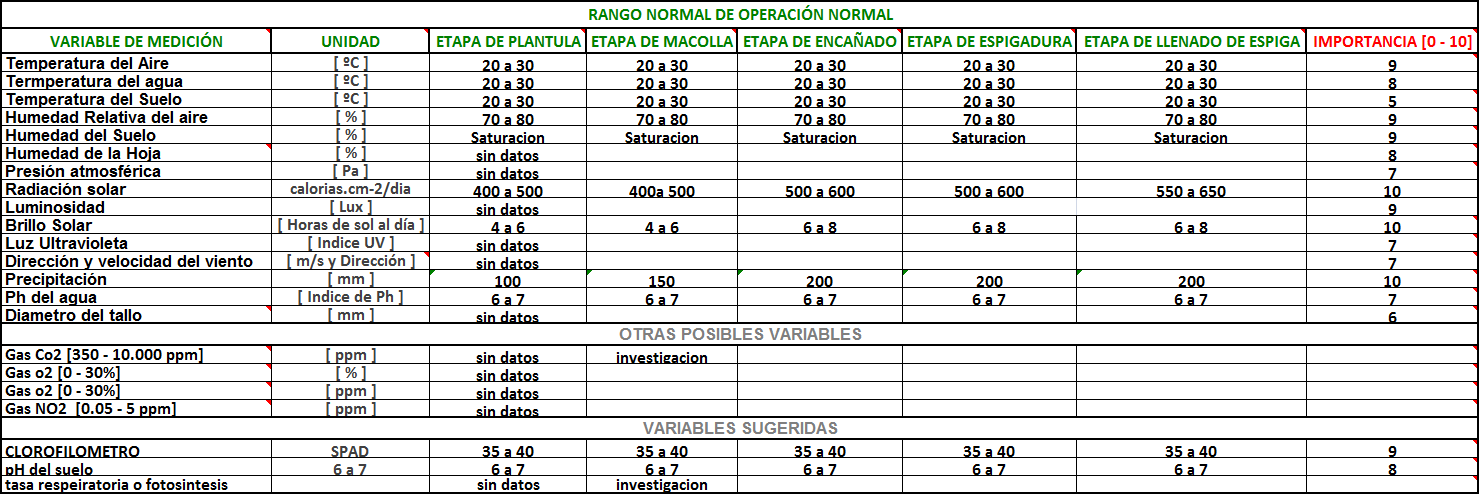
Media/Tabla_Fedearroz.png
