HaroldMurcia/AgroSenseV1.0/Media/Tapa_ACD_0.jpg

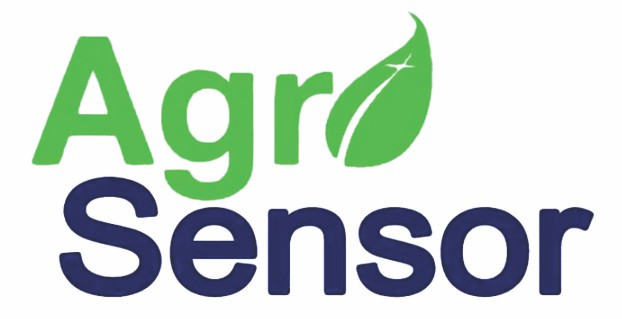
Media/Tapa_ACD_0.jpg
