HaroldMurcia/AgroSenseV1.0/Media/Tapa_ACD_1.jpg

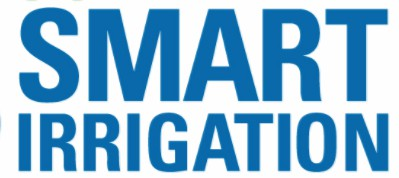
Media/Tapa_ACD_1.jpg
