HaroldMurcia/AgroSenseV1.0/Media/Tarjeta3D.jpg

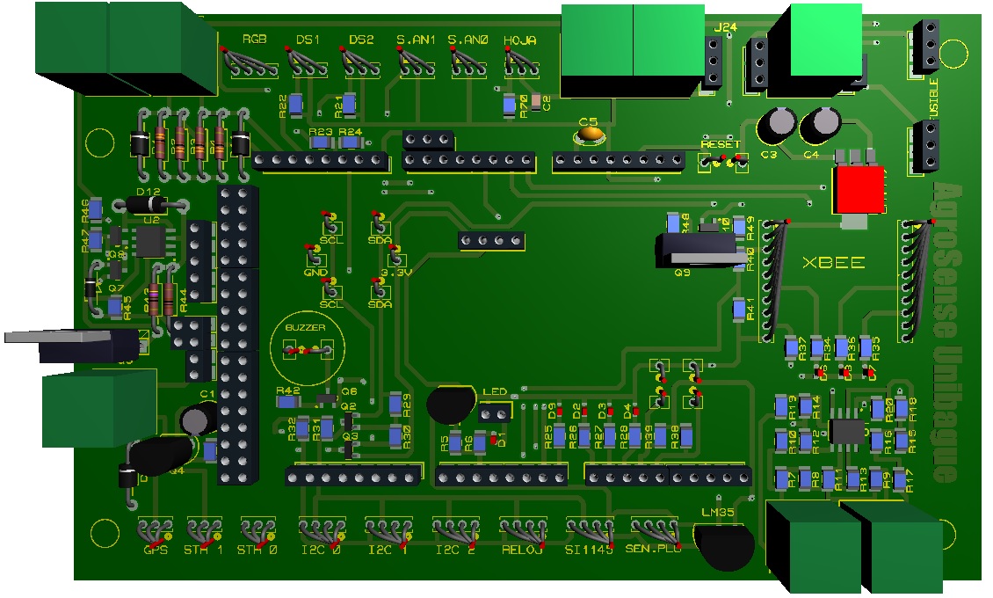
Media/Tarjeta3D.jpg
