HaroldMurcia/AgroSenseV1.0/Media/ThingSpeak/Captura thingspeak2.png

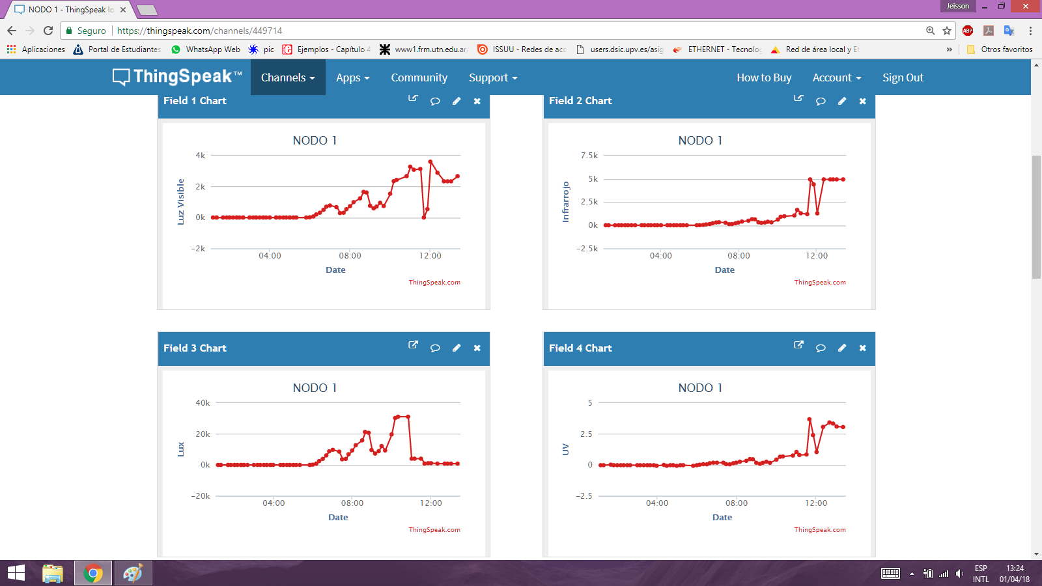
Media/ThingSpeak/Captura thingspeak2.png
