HaroldMurcia/AgroSenseV1.0/Media/ThingSpeak/Captura thingspeak.png

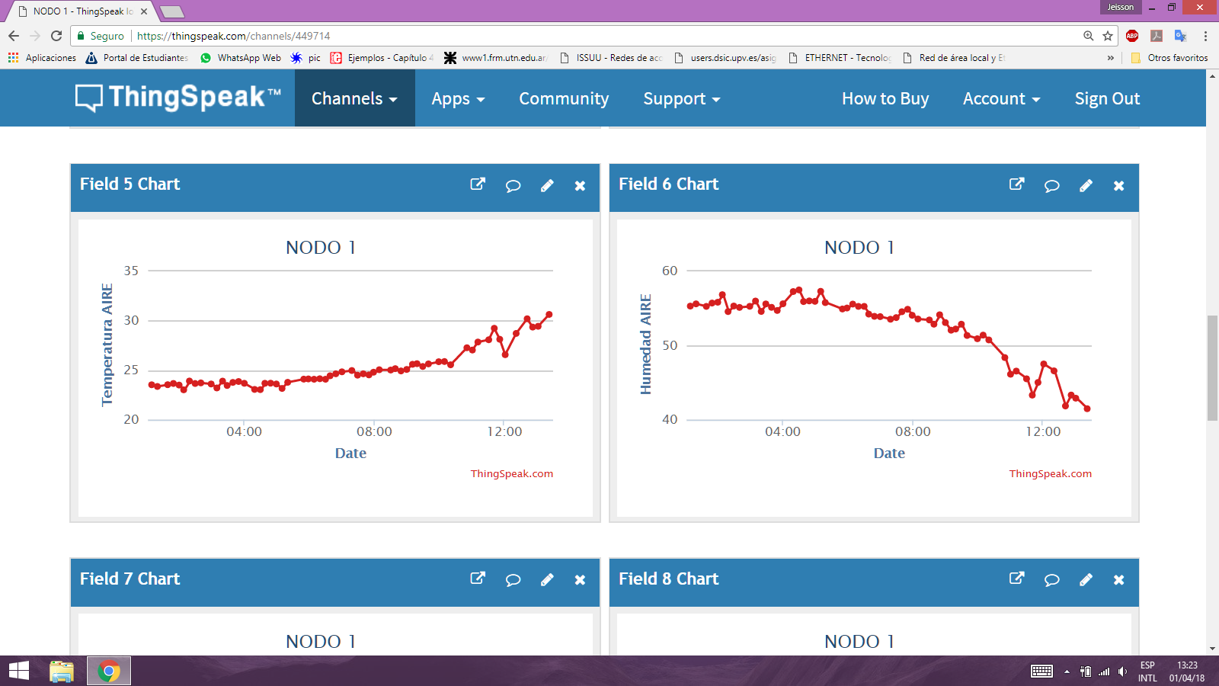
Media/ThingSpeak/Captura thingspeak.png
