HaroldMurcia/AgroSenseV1.0/Media/ThingSpeak/Captura_Hum_Air_1.jpg

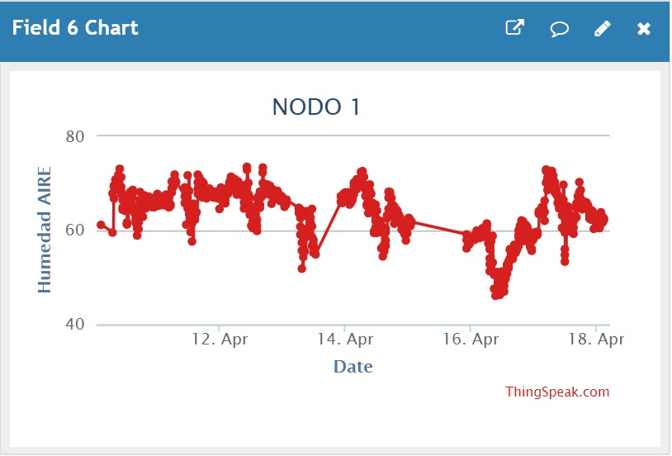
Media/ThingSpeak/Captura_Hum_Air_1.jpg
