HaroldMurcia/AgroSenseV1.0/Media/ThingSpeak/Captura_Hum_Air_2.jpg

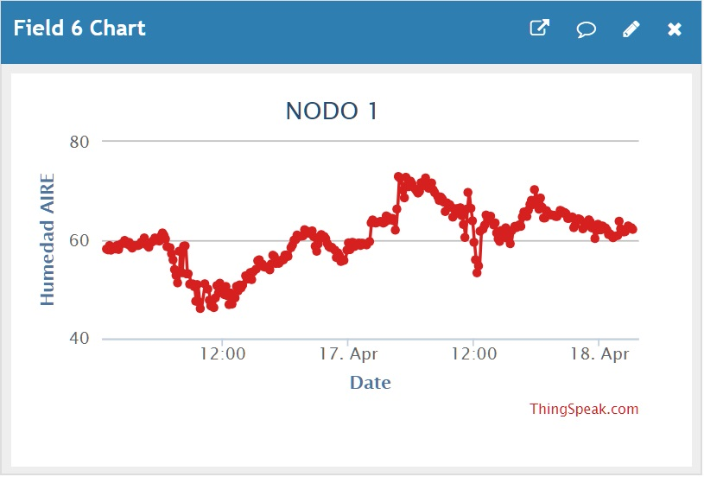
Media/ThingSpeak/Captura_Hum_Air_2.jpg
