HaroldMurcia/AgroSenseV1.0/Media/ThingSpeak/Captura_Hum_Air_3.jpg

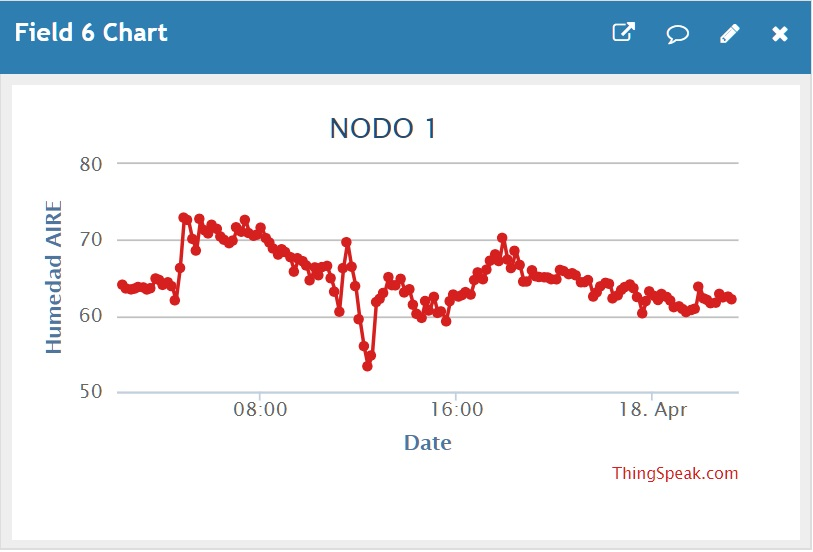
Media/ThingSpeak/Captura_Hum_Air_3.jpg
