HaroldMurcia/AgroSenseV1.0/Media/ThingSpeak/Captura_Inf_1.jpg

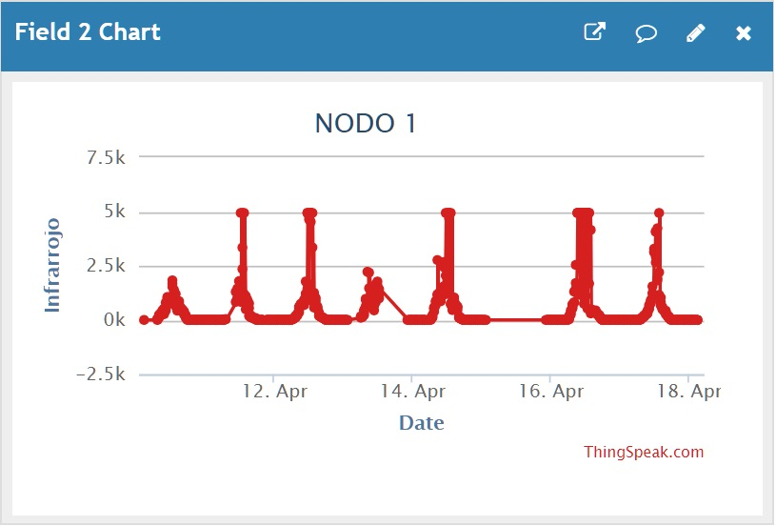
Media/ThingSpeak/Captura_Inf_1.jpg
