HaroldMurcia/AgroSenseV1.0/Media/ThingSpeak/Captura_Inf_2.jpg

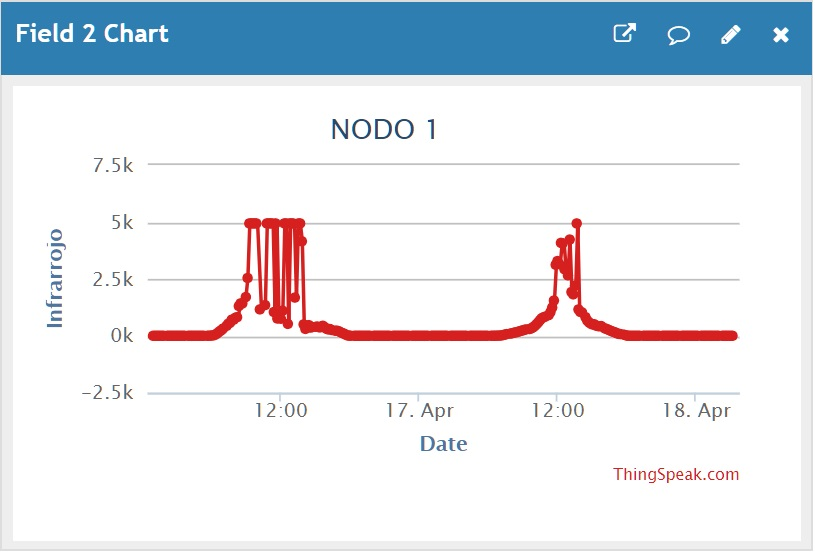
Media/ThingSpeak/Captura_Inf_2.jpg
