HaroldMurcia/AgroSenseV1.0/Media/ThingSpeak/Captura_Inf_3.jpg

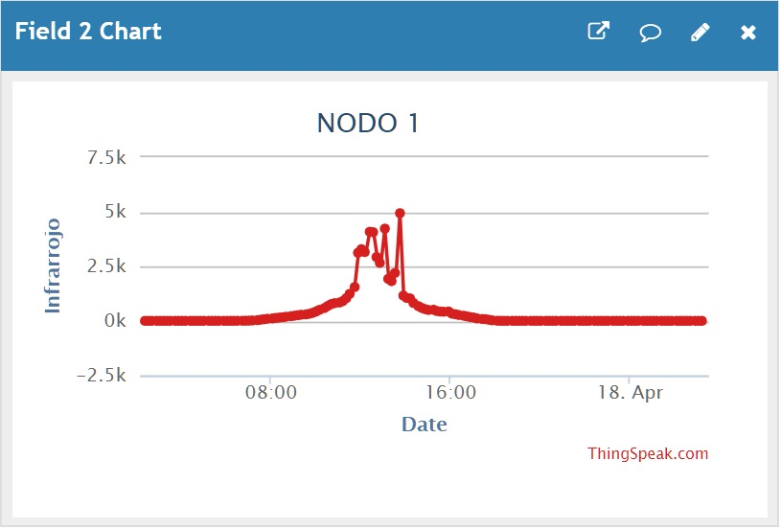
Media/ThingSpeak/Captura_Inf_3.jpg
