HaroldMurcia/AgroSenseV1.0/Media/ThingSpeak/Captura_Lux_1.jpg

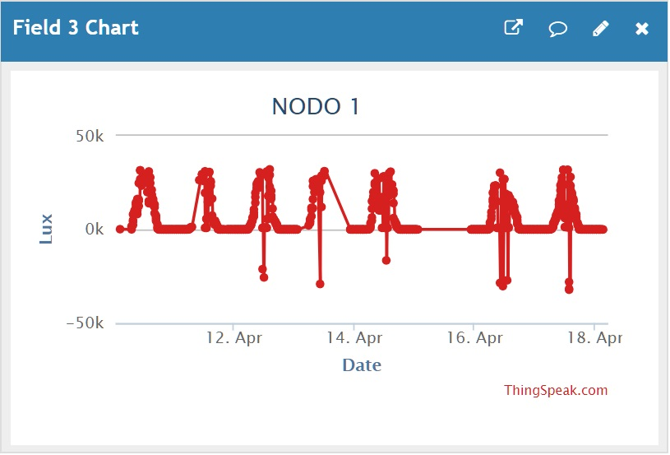
Media/ThingSpeak/Captura_Lux_1.jpg
