HaroldMurcia/AgroSenseV1.0/Media/ThingSpeak/Captura_Lux_2.jpg

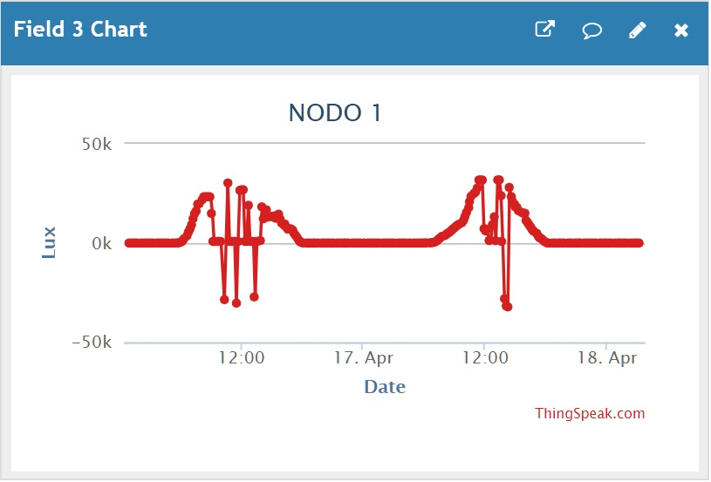
Media/ThingSpeak/Captura_Lux_2.jpg
