HaroldMurcia/AgroSenseV1.0/Media/ThingSpeak/Captura_Lux_3 - copia.jpg

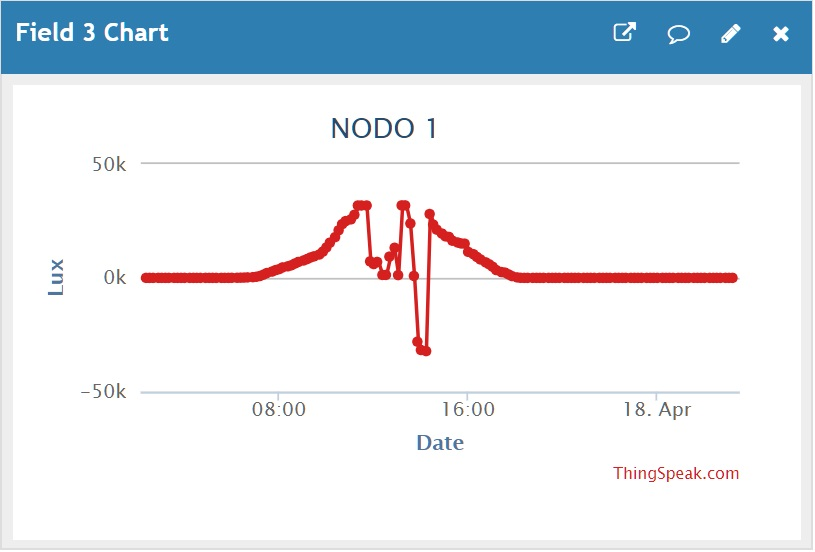
Media/ThingSpeak/Captura_Lux_3 - copia.jpg
