HaroldMurcia/AgroSenseV1.0/Media/ThingSpeak/Captura_Luz_Vis_3 - copia.jpg

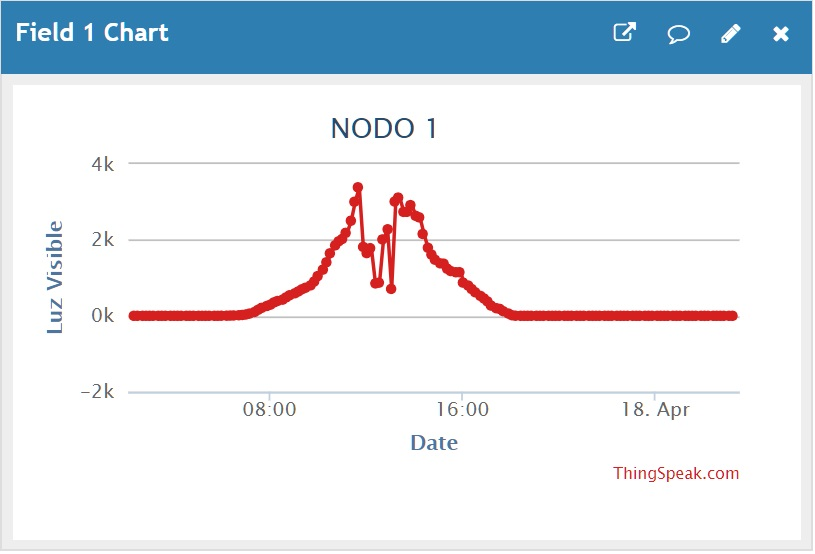
Media/ThingSpeak/Captura_Luz_Vis_3 - copia.jpg
