HaroldMurcia/AgroSenseV1.0/Media/ThingSpeak/Captura_Smp_1.jpg

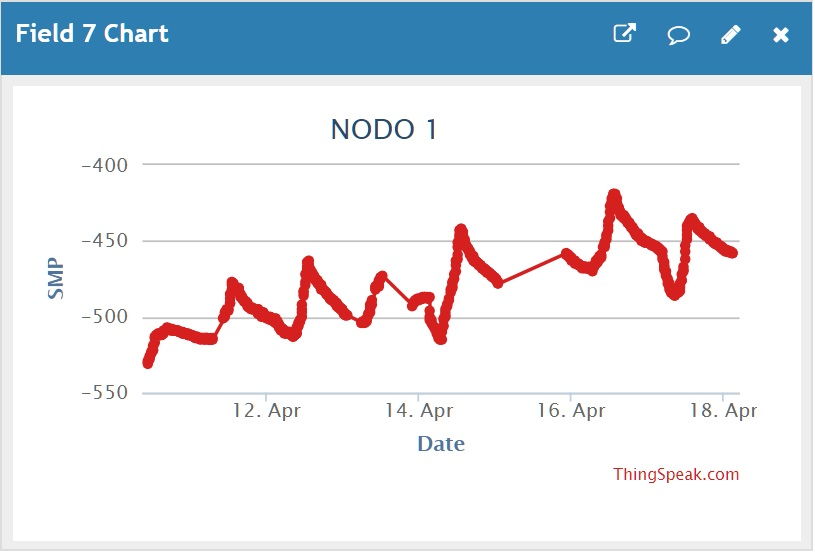
Media/ThingSpeak/Captura_Smp_1.jpg
