HaroldMurcia/AgroSenseV1.0/Media/ThingSpeak/Captura_Smp_2.jpg

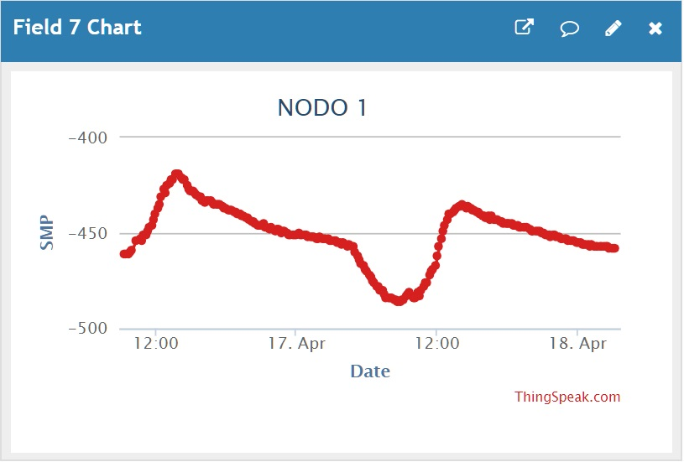
Media/ThingSpeak/Captura_Smp_2.jpg
