HaroldMurcia/AgroSenseV1.0/Media/ThingSpeak/Captura_Smp_3.jpg

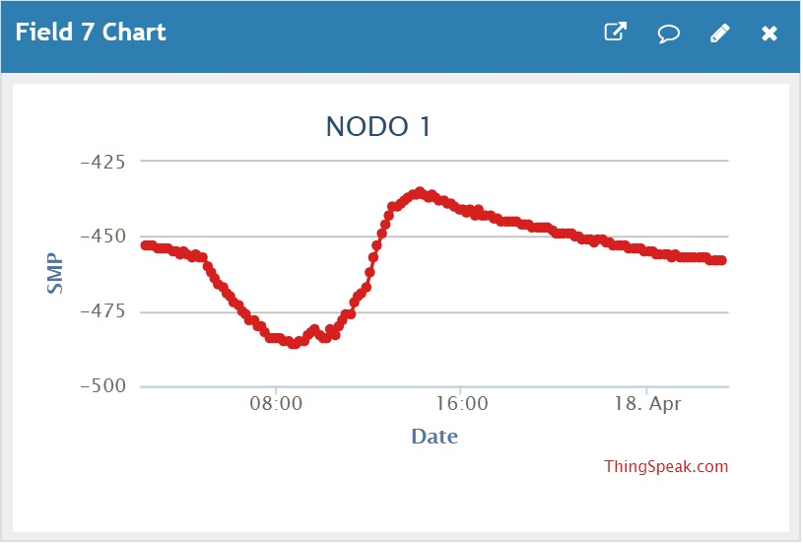
Media/ThingSpeak/Captura_Smp_3.jpg
