HaroldMurcia/AgroSenseV1.0/Media/ThingSpeak/Captura_Tem_Air_3.jpg

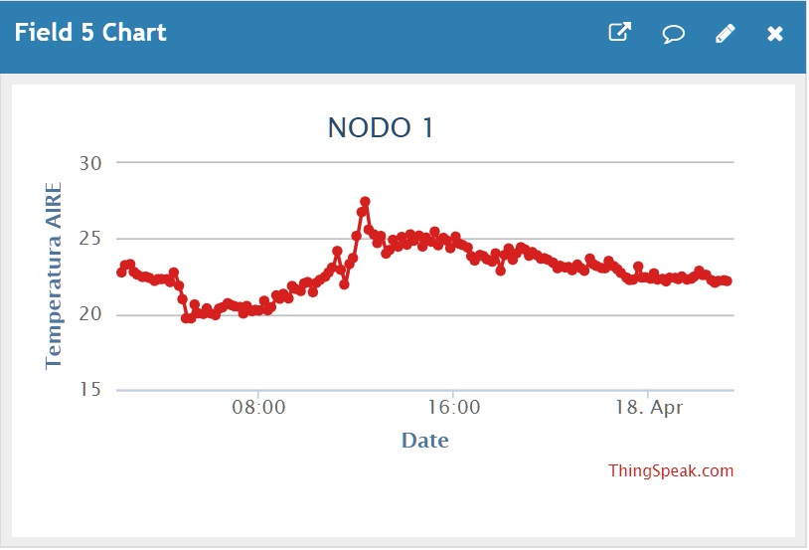
Media/ThingSpeak/Captura_Tem_Air_3.jpg
