HaroldMurcia/AgroSenseV1.0/Media/ThingSpeak/Captura_Tem_Sue_2.jpg

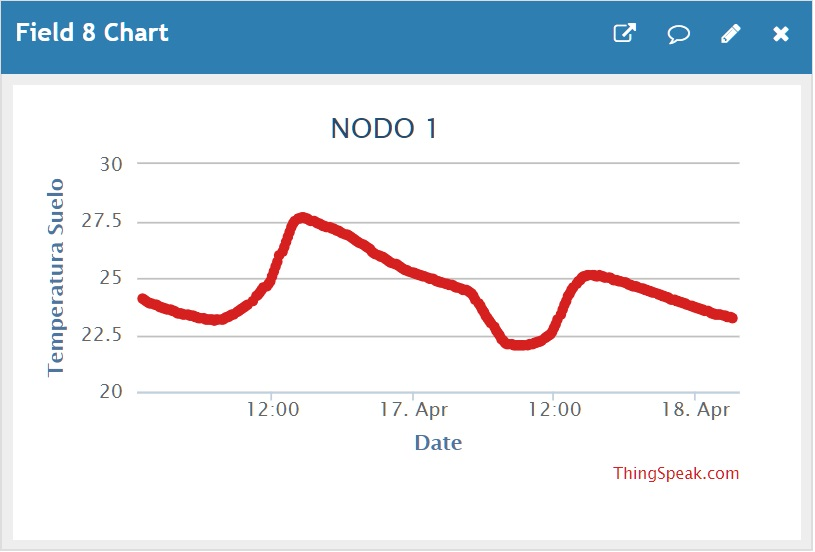
Media/ThingSpeak/Captura_Tem_Sue_2.jpg
