HaroldMurcia/AgroSenseV1.0/Media/ThingSpeak/Captura_Uv_1.jpg

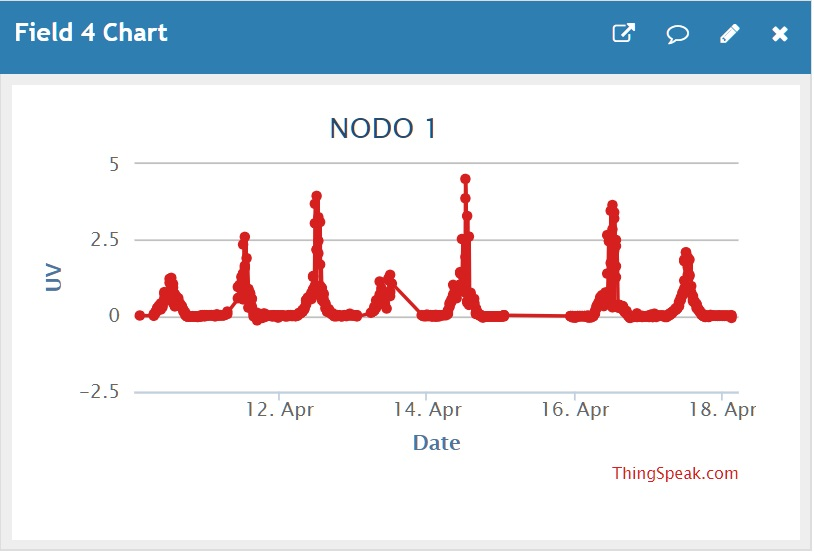
Media/ThingSpeak/Captura_Uv_1.jpg
