HaroldMurcia/AgroSenseV1.0/Media/ThingSpeak/Captura_Uv_2.jpg

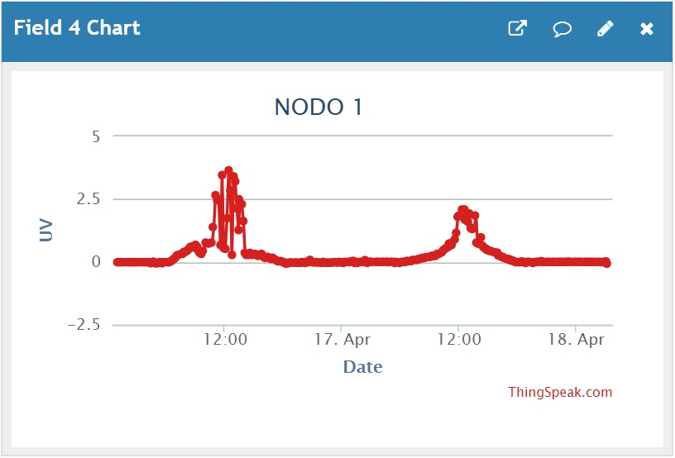
Media/ThingSpeak/Captura_Uv_2.jpg
