HaroldMurcia/AgroSenseV1.0/Media/ThingSpeak/Captura_Uv_3.jpg

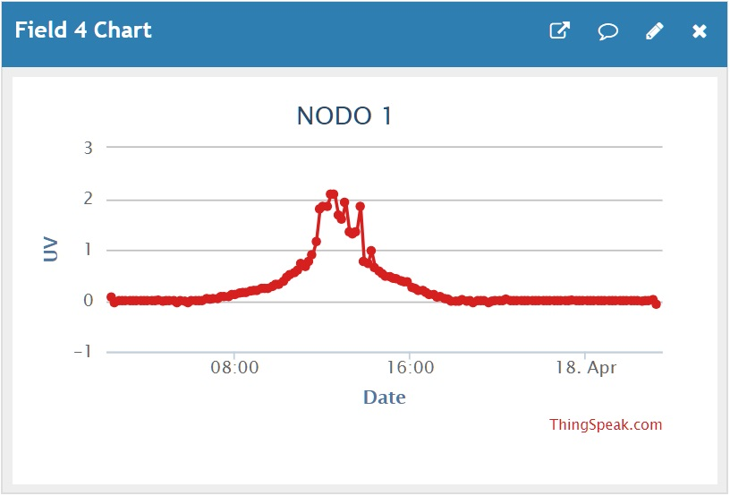
Media/ThingSpeak/Captura_Uv_3.jpg
