HaroldMurcia/AgroSenseV1.0/Media/ThingSpeak/GPS.jpg

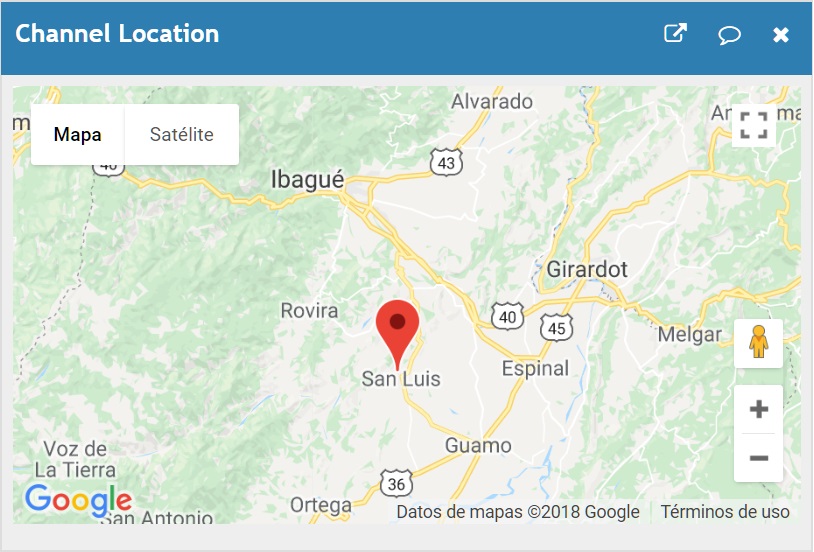
Media/ThingSpeak/GPS.jpg
