HaroldMurcia/AgroSenseV1.0/Media/ThingSpeak/Sin título1.png

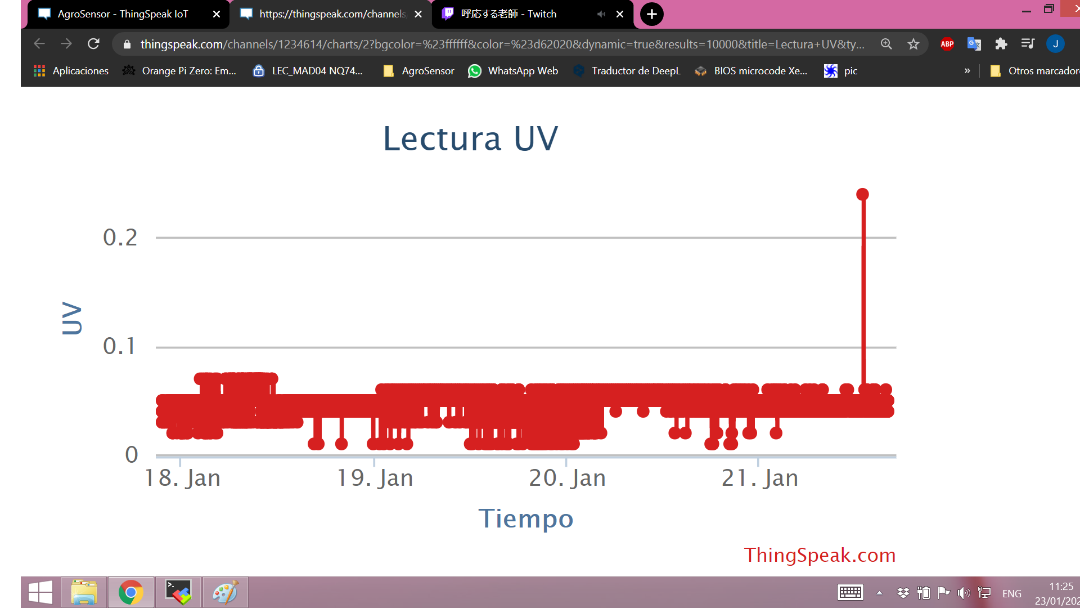
Media/ThingSpeak/Sin título1.png
