HaroldMurcia/AgroSenseV1.0/Media/ThingSpeak/Sin título2.png

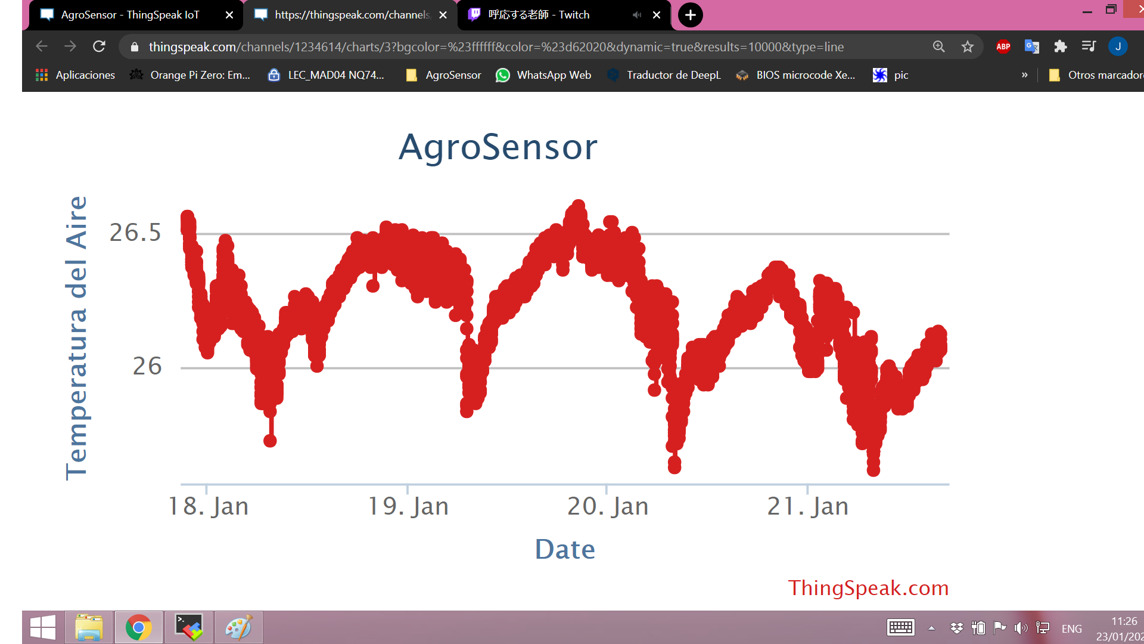
Media/ThingSpeak/Sin título2.png
