HaroldMurcia/AgroSenseV1.0/Media/ThingSpeak/Sin título3.png

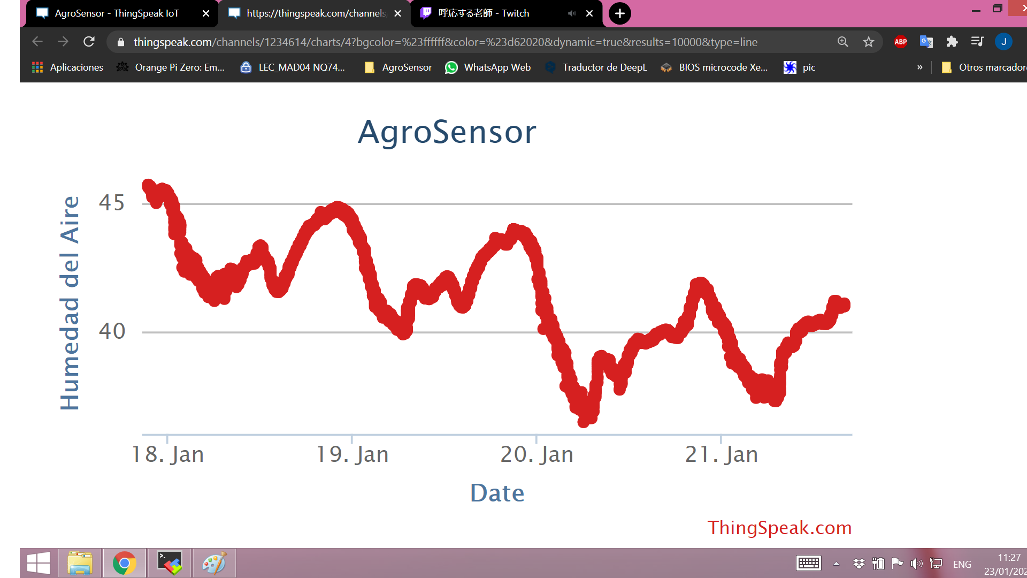
Media/ThingSpeak/Sin título3.png
