HaroldMurcia/AgroSenseV1.0/Media/ThingSpeak/Sin título4.png

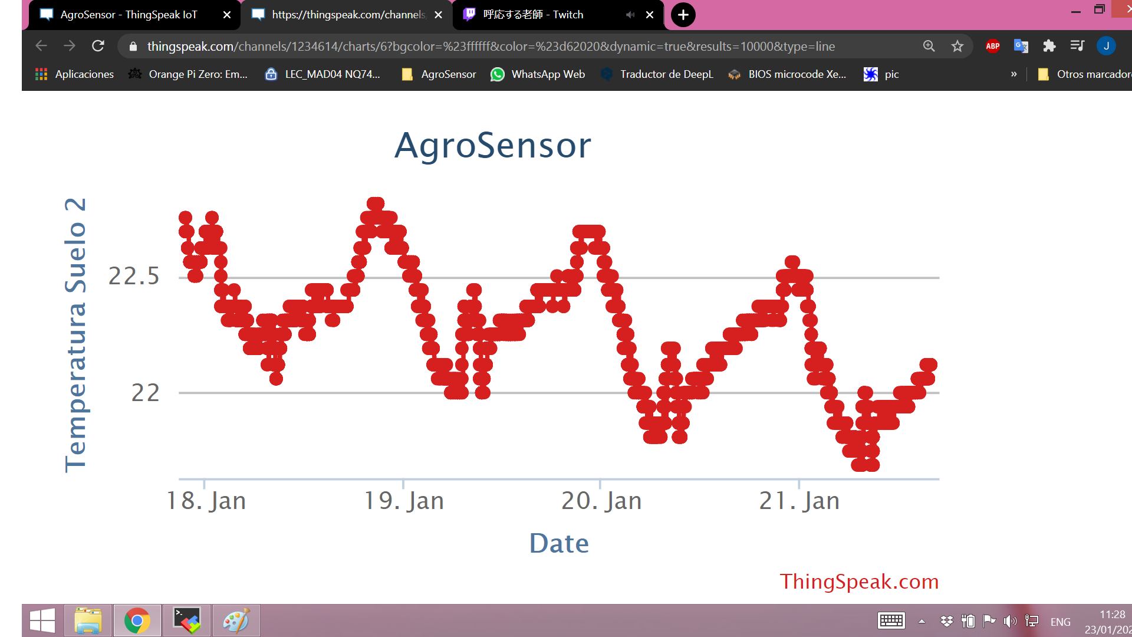
Media/ThingSpeak/Sin título4.png
