HaroldMurcia/AgroSenseV1.0/Media/ThingSpeak/Sin título5.png

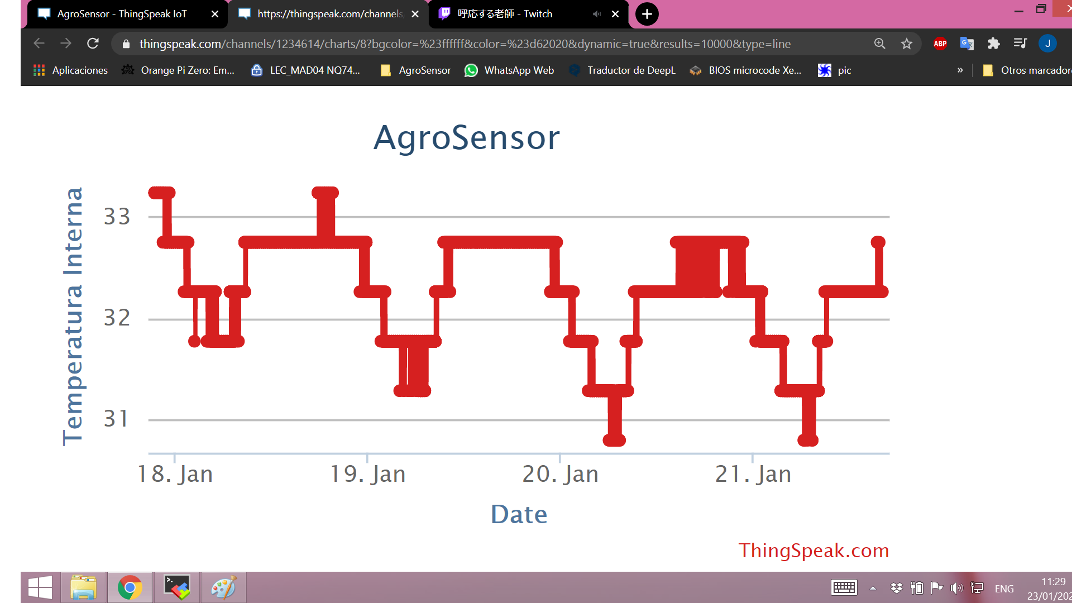
Media/ThingSpeak/Sin título5.png
