HaroldMurcia/AgroSenseV1.0/Media/ThingSpeak/Sin título6.png

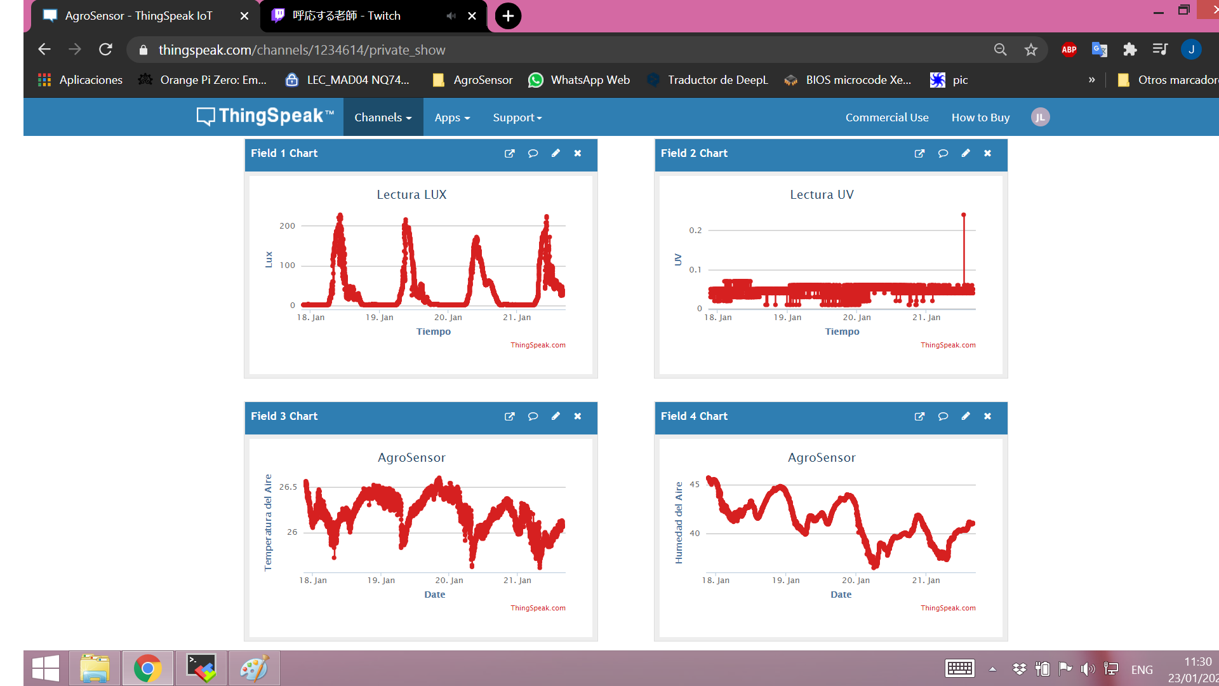
Media/ThingSpeak/Sin título6.png
