HaroldMurcia/AgroSenseV1.0/Media/ThingSpeak/Sin título7.png

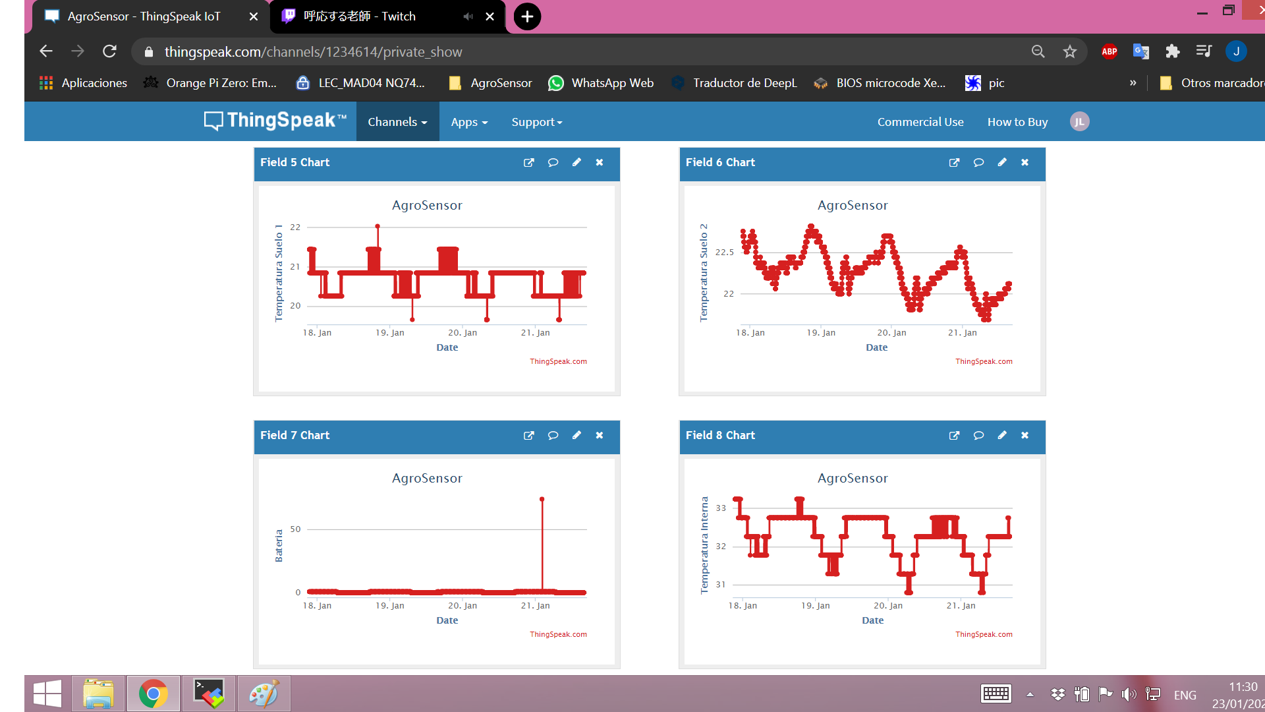
Media/ThingSpeak/Sin título7.png
