HaroldMurcia/AgroSenseV1.0/Media/ThingSpeak/Sin título8.png

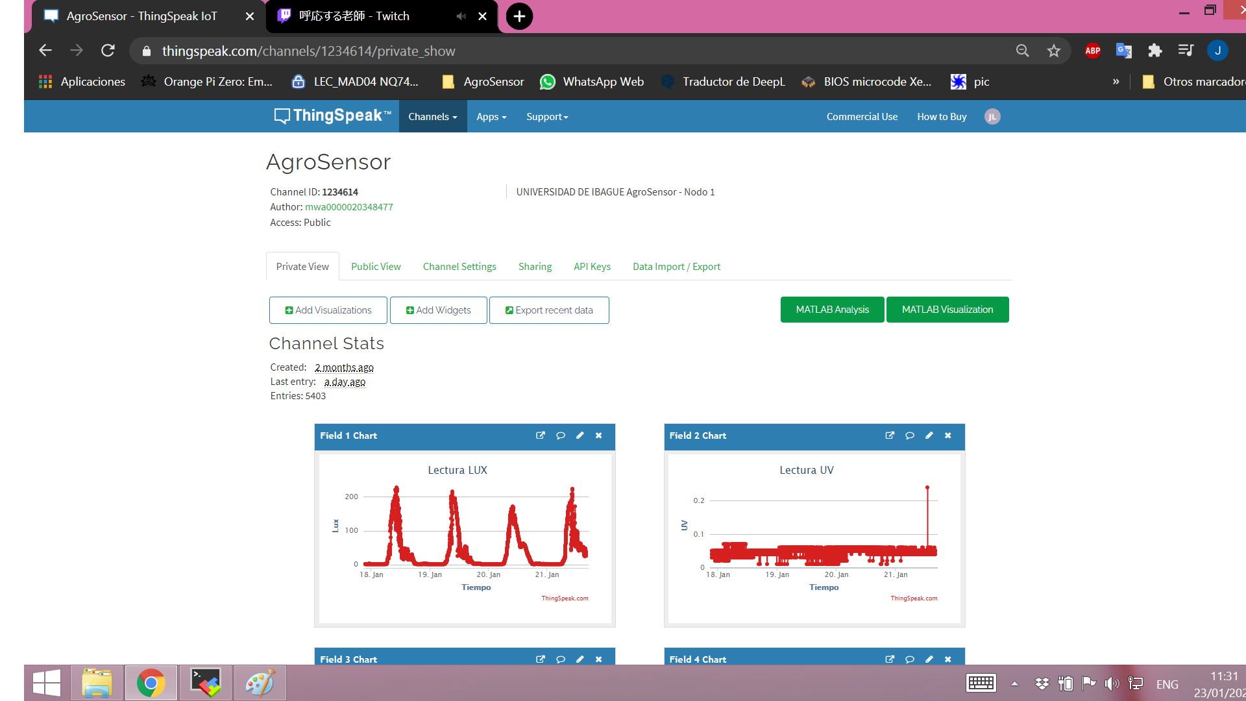
Media/ThingSpeak/Sin título8.png
