HaroldMurcia/AgroSenseV1.0/Media/ThingSpeak/Sin título.png

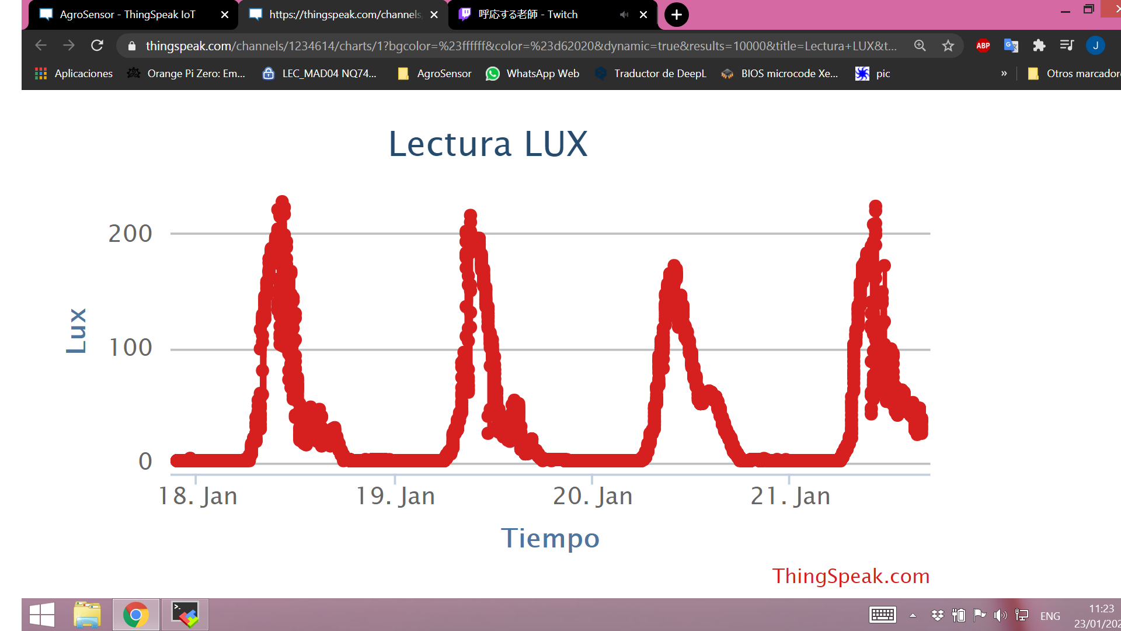
Media/ThingSpeak/Sin título.png
