HaroldMurcia/AgroSenseV1.0/Media/XBEE.jpg

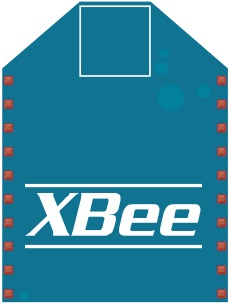
Media/XBEE.jpg
