HaroldMurcia/AgroSenseV1.0/Diseño/Diseño Tarjeta/PCB Proteus/AgroSensor V1 PCB/Mascaras/medidas.pdf

## SI2C

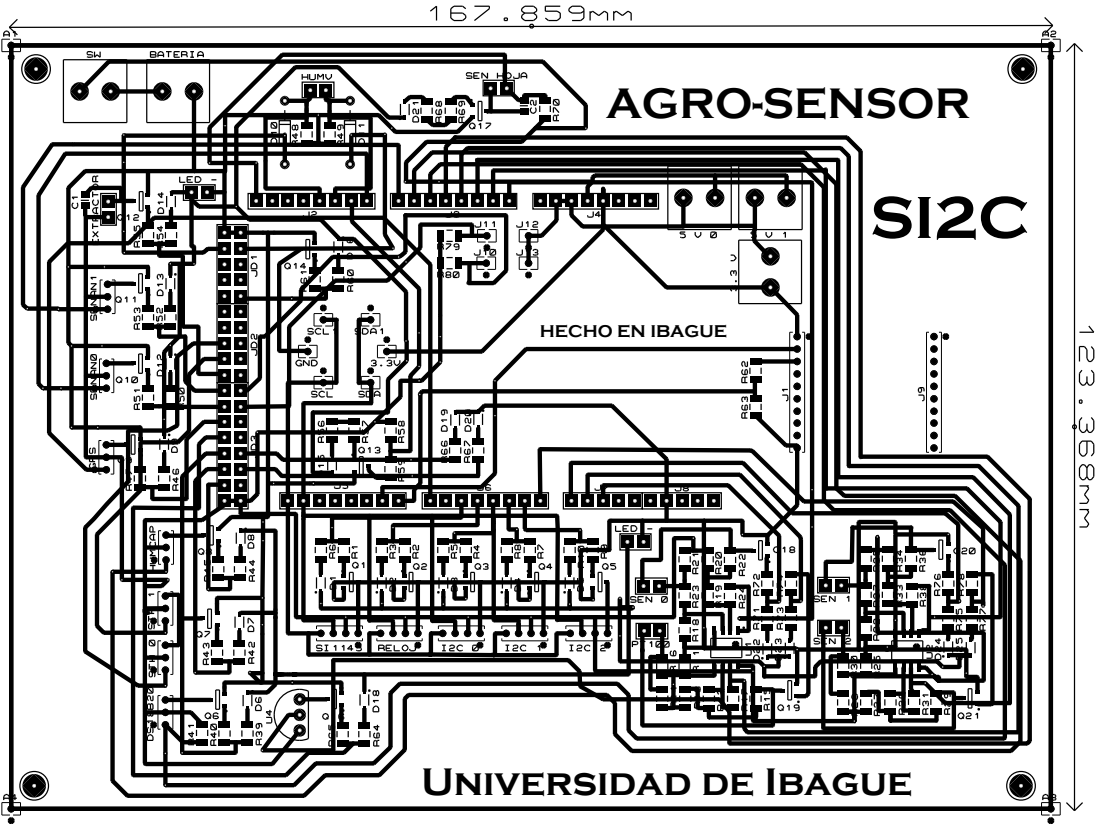
[picture p153: page 1]
AGRO-SENSOR

HECHO EN IBAGUE

Universidad de Ibague
