HaroldMurcia/AgroSenseV1.0/Diseño/Diseño Tarjeta/PCB Proteus/AgroSensor V1 PCB/Mascaras/SILK2.PDF

## AGRO-SENSOR

## SI2C

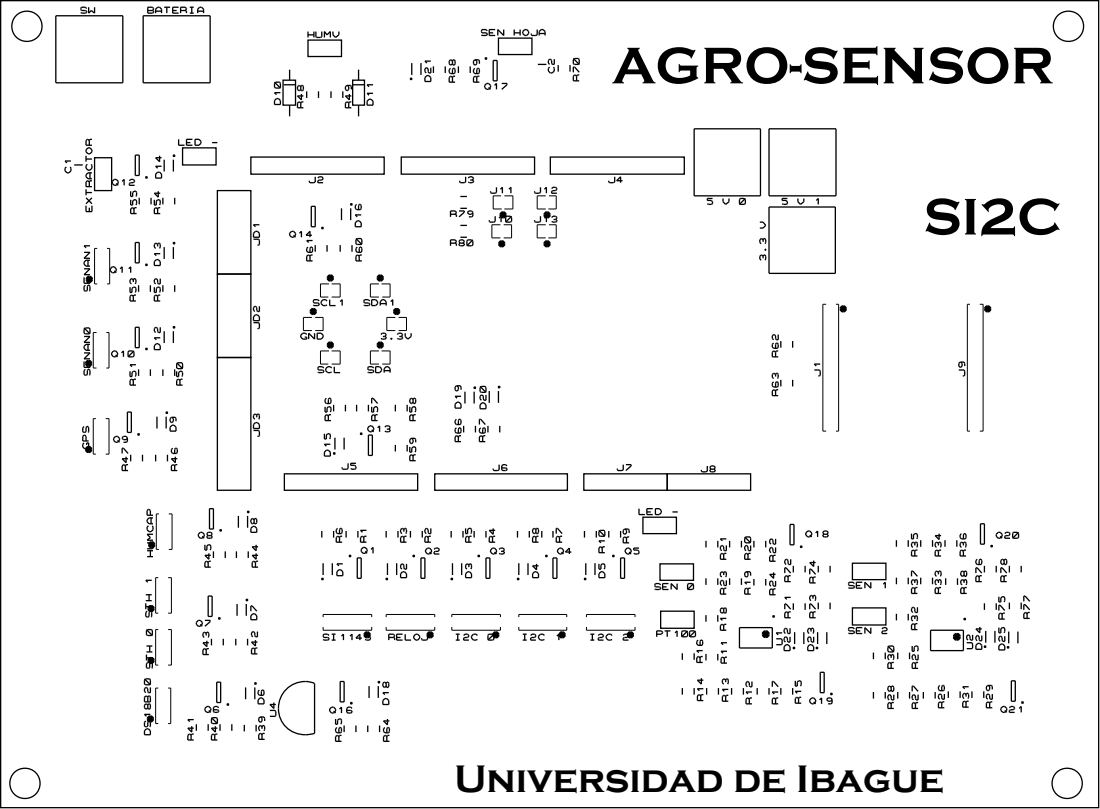
[picture p154: page 1]

Universidad de Ibague
