HaroldMurcia/AgroSenseV1.0/Diseño/Diseño Tarjeta/PCB Proteus/AgroSensor V1 PCB/Mascaras/top.pdf

## SI2C

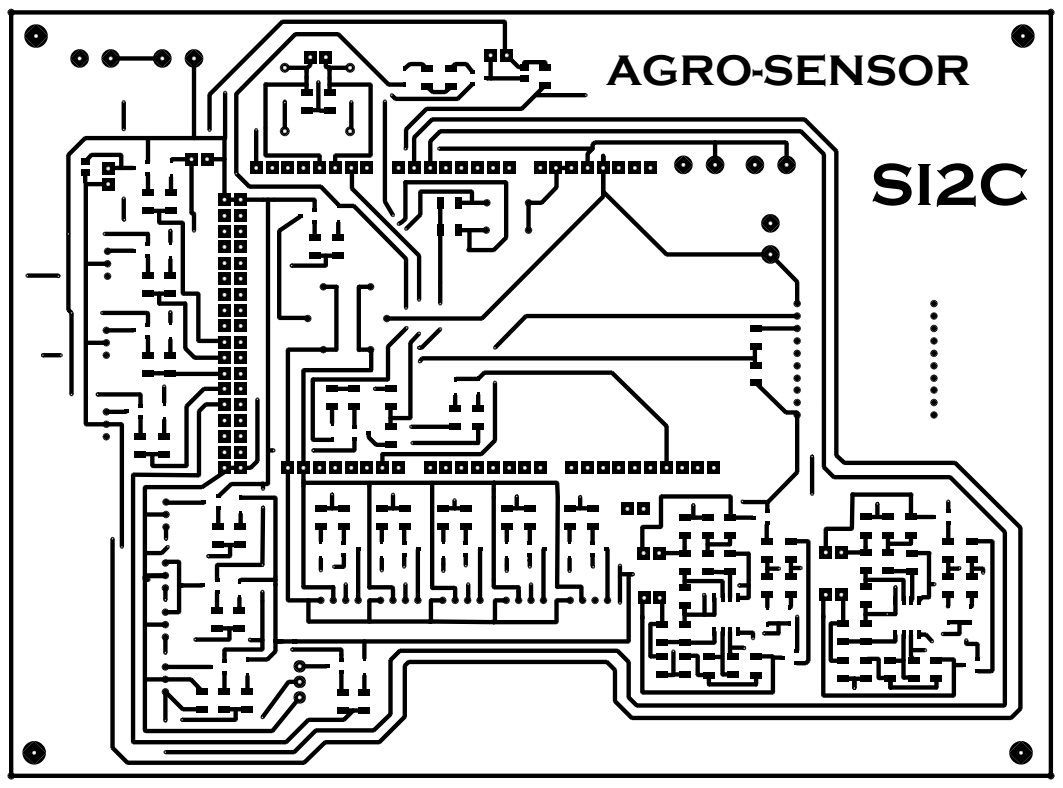
[picture p155: page 1]
AGRO-SENSOR
