HaroldMurcia/AgroSenseV1.0/Diseño/Diseño Tarjeta/PCB Proteus/AgroSensor V2 PCB/New Project.PDF

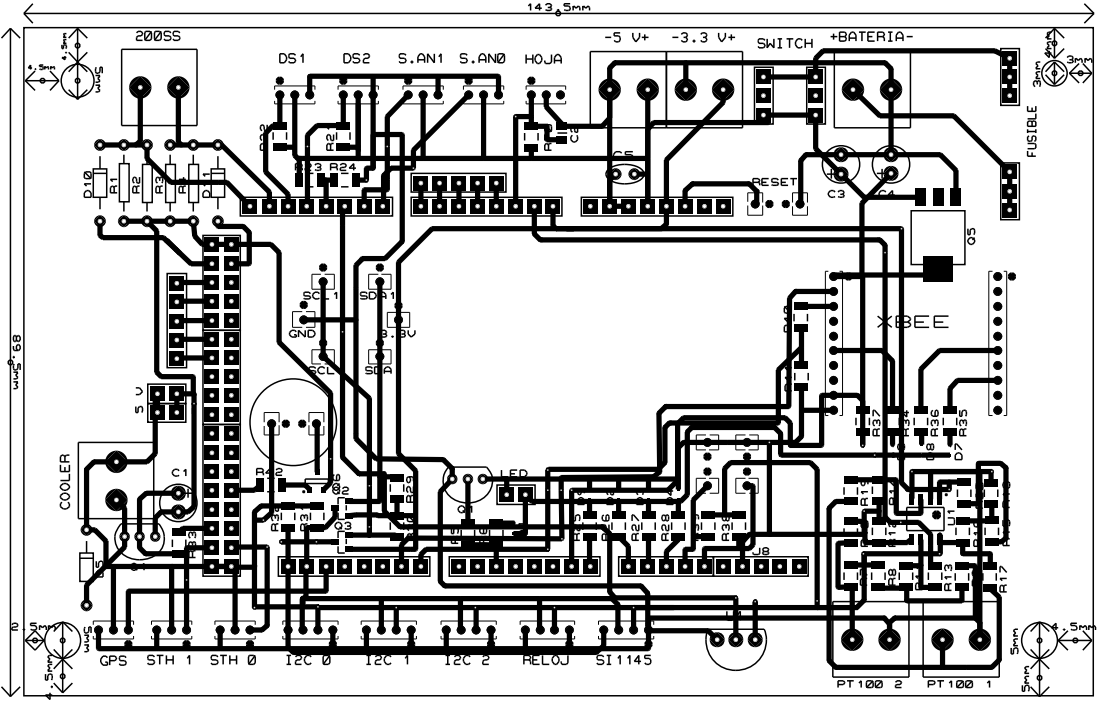
[picture p156: page 1]
