HaroldMurcia/AgroSenseV1.0/Diseño/Diseño Tarjeta/PCB Proteus/AgroSensor V1 PCB/Mascaras/bot.pdf

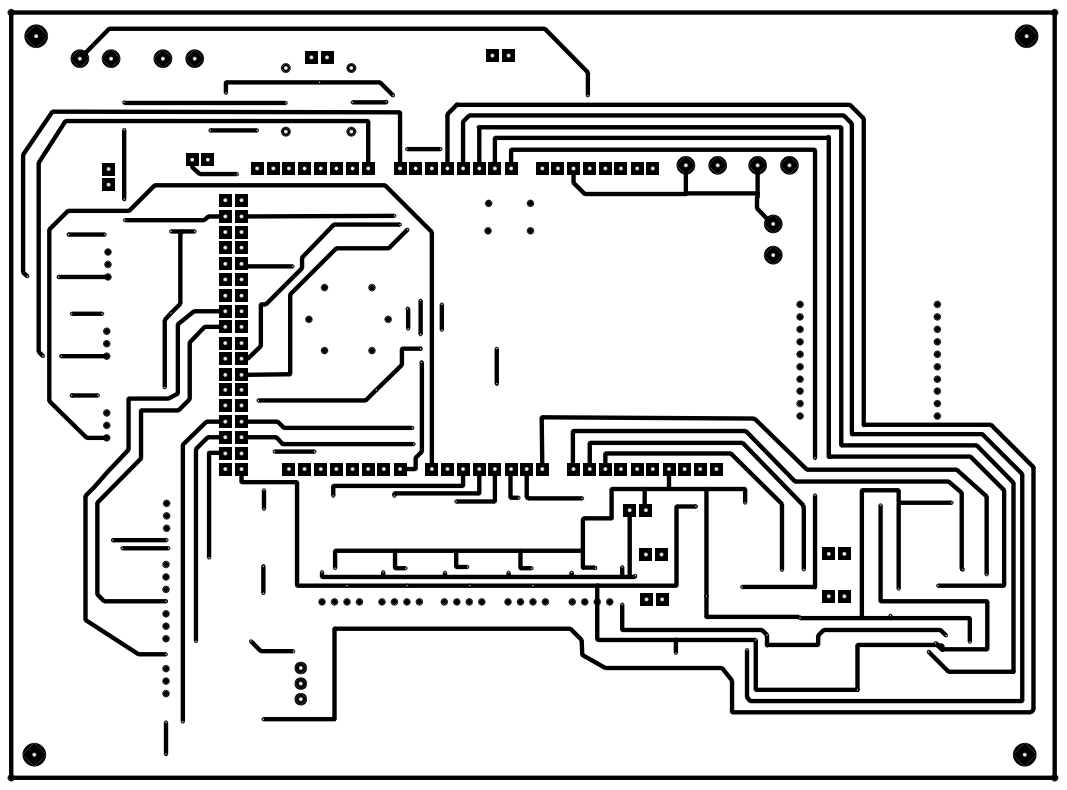
[picture p157: page 1]
