HaroldMurcia/AgroSenseV1.0/Diseño/Diseño Tarjeta/PCB Proteus/AgroSensor V1 PCB/Mascaras/BOT2.PDF

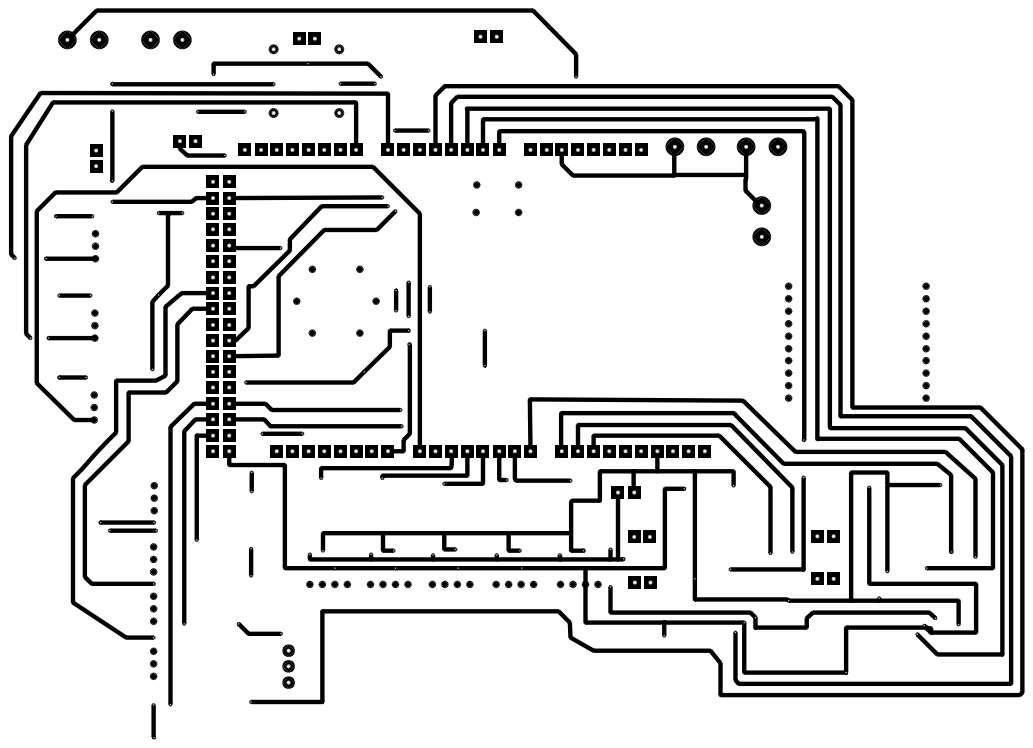
[picture p158: page 1]
