HaroldMurcia/AgroSenseV1.0/Diseño/Diseño Tarjeta/PCB Proteus/AgroSensor V1 PCB/Mascaras/silk.pdf

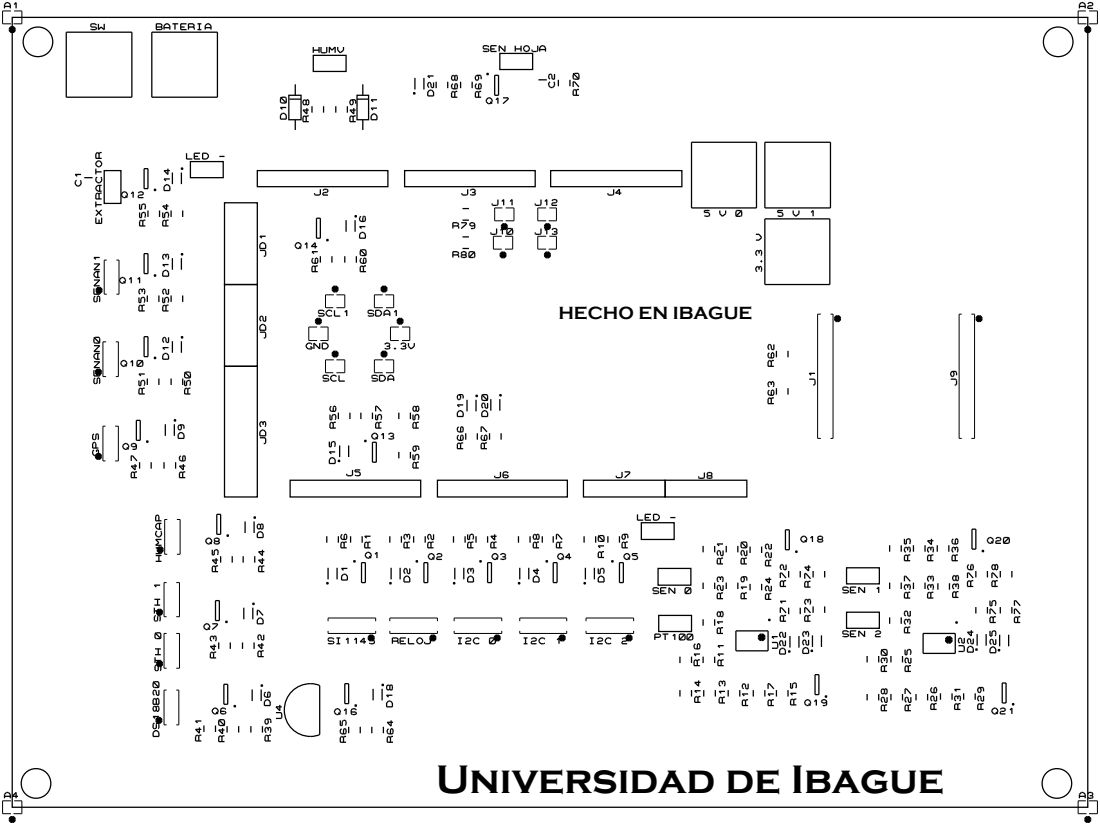
[picture p159: page 1]

HECHO EN IBAGUE

Universidad de Ibague
