HaroldMurcia/AgroSenseV1.0/Diseño/Diseño Tarjeta/PCB Proteus/AgroSensor V1 PCB/Mascaras/TarjetaPCB.PDF

## AGRO-ENSOR

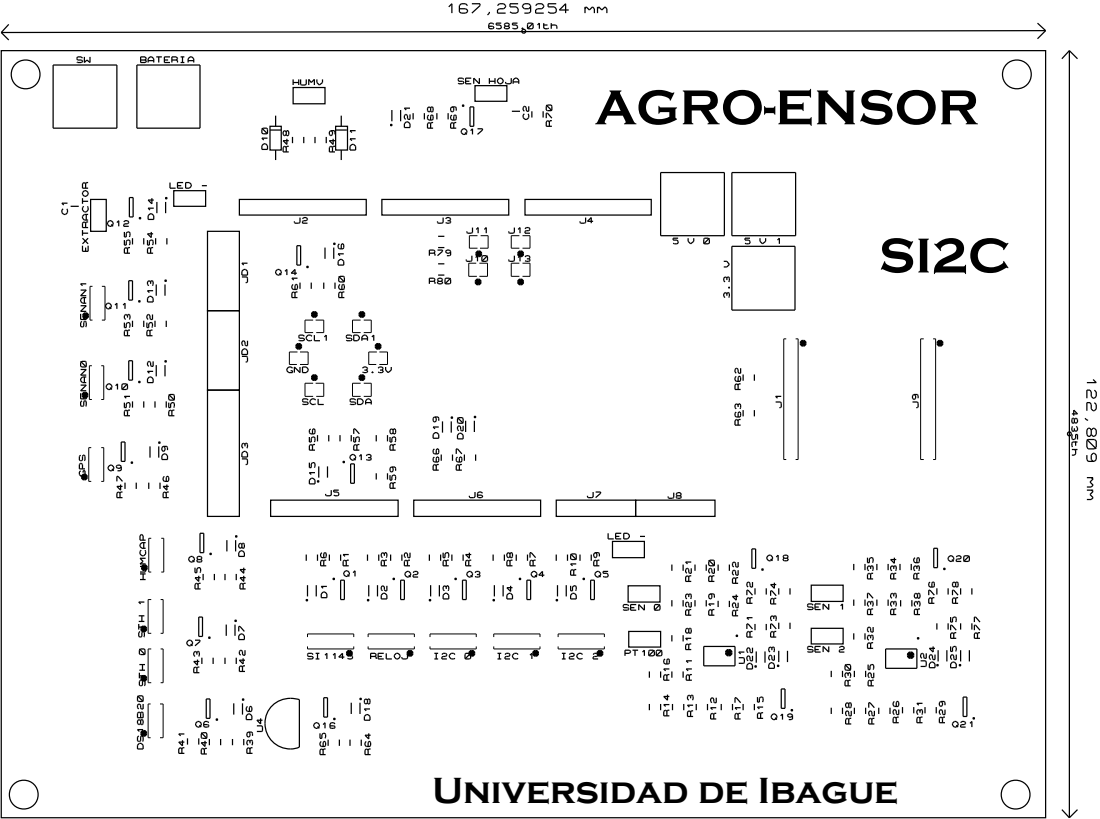
[picture p160: page 1]

Universidad de Ibague
